kimbring2/DeepSoccer/deepsoccer_jetson/image/NX_DC_Motor.png

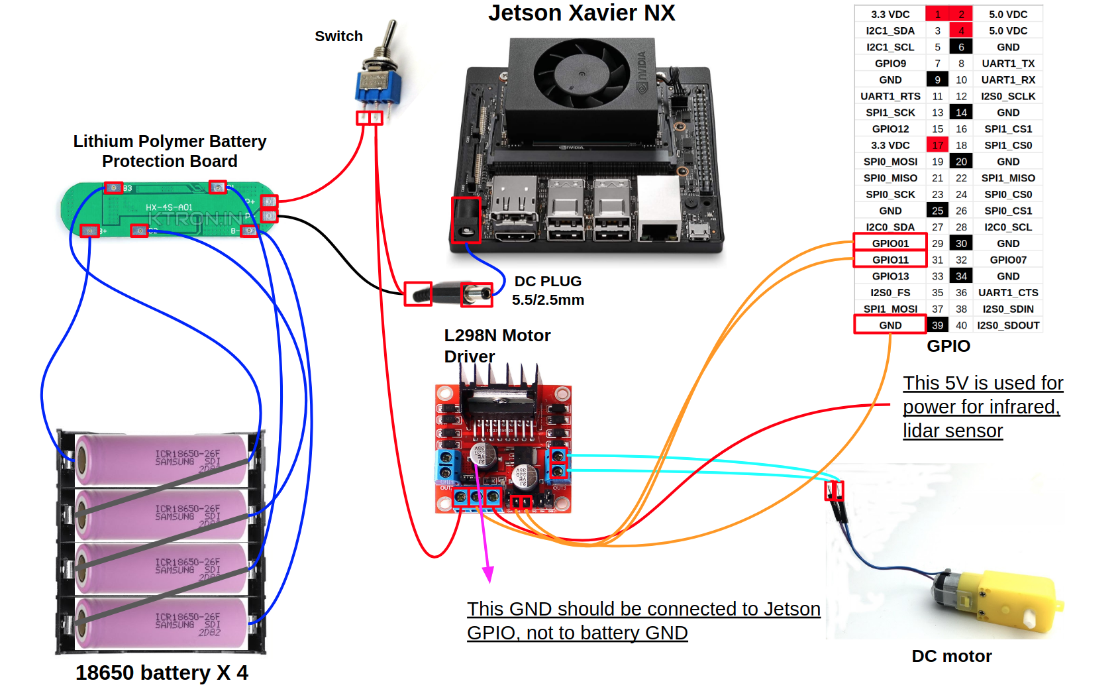
deepsoccer_jetson/image/NX_DC_Motor.png
