kimbring2/DeepSoccer/deepsoccer_jetson/image/NX_Dynamixel.png

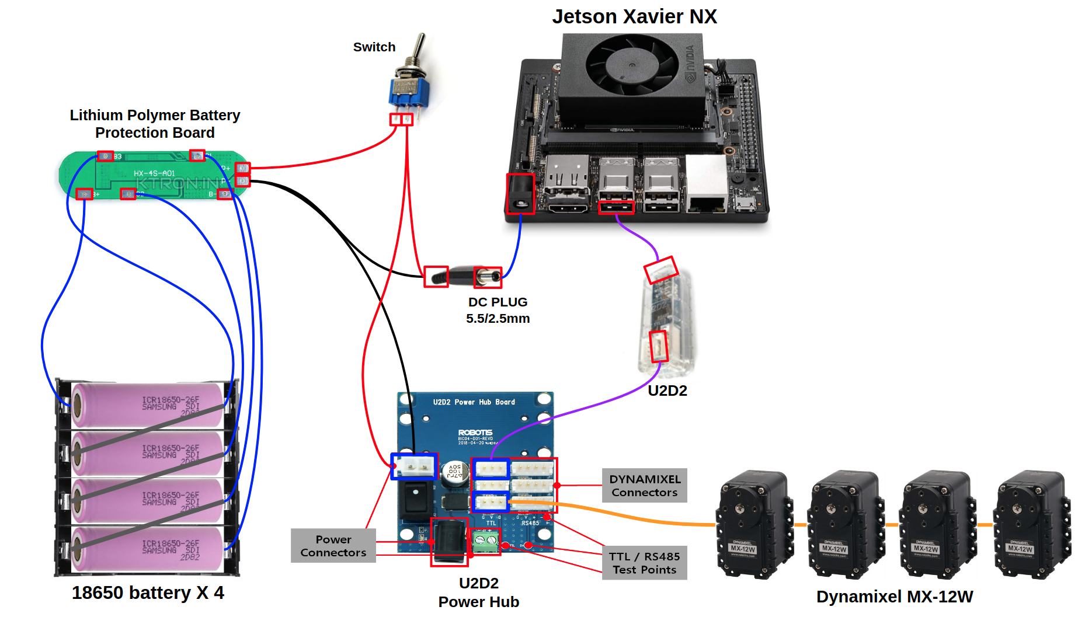
deepsoccer_jetson/image/NX_Dynamixel.png
