kimbring2/DeepSoccer/image/ADE_train_00006856.jpg

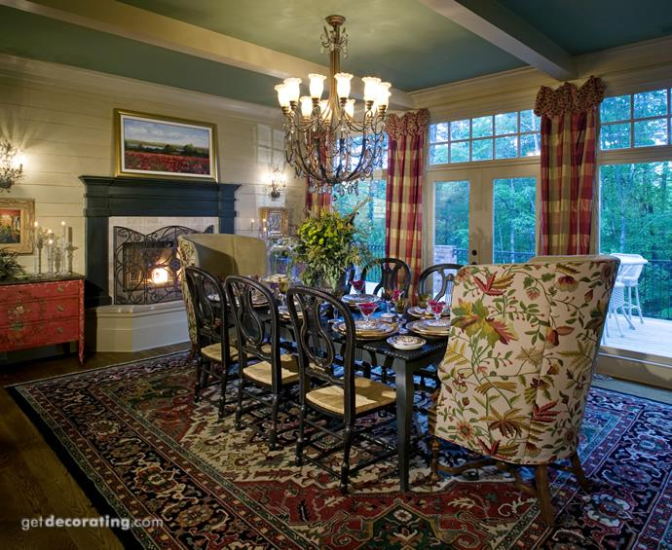
image/ADE_train_00006856.jpg
