kimbring2/DeepSoccer/image/ADE_train_00006856_seg.png

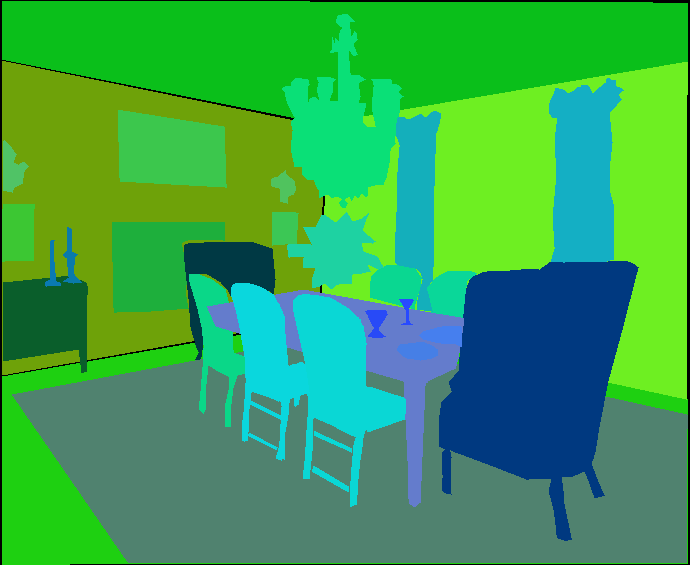
image/ADE_train_00006856_seg.png
