kimbring2/DeepSoccer/image/ADE_train_00006856_seg_simple.png

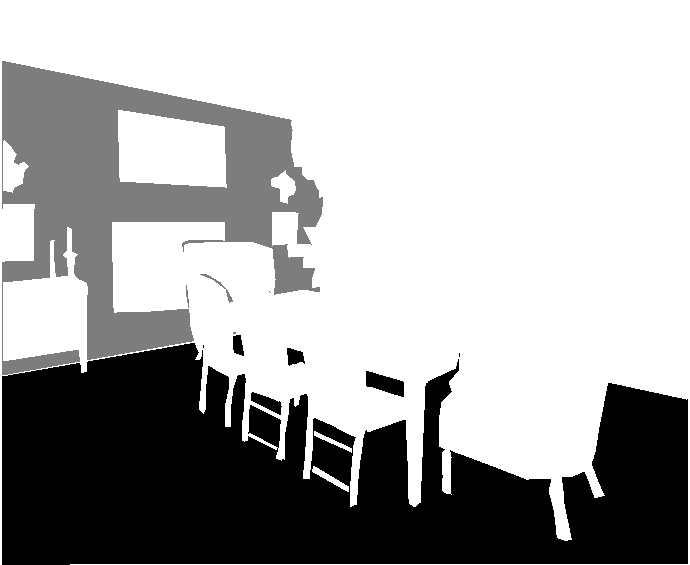
image/ADE_train_00006856_seg_simple.png
