kimbring2/DeepSoccer/image/controller_error.png

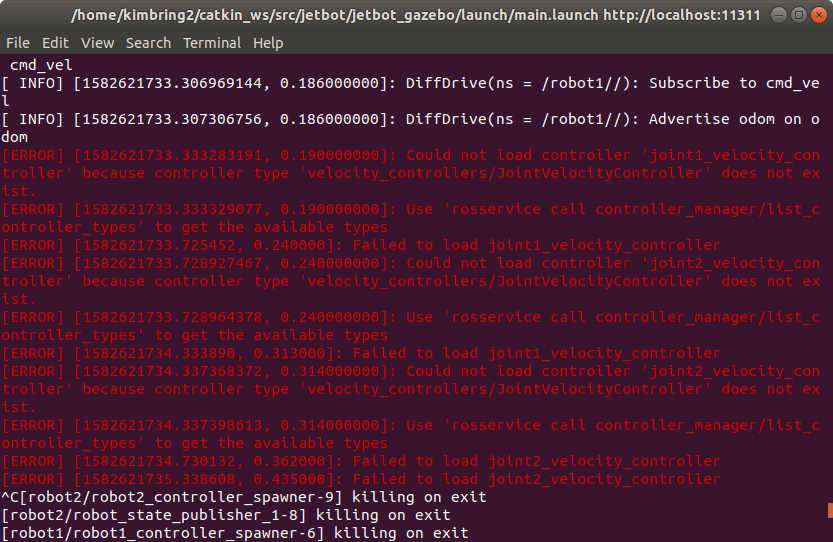
image/controller_error.png
