kimbring2/DeepSoccer/image/CycleGAN_wrong_case_4.png

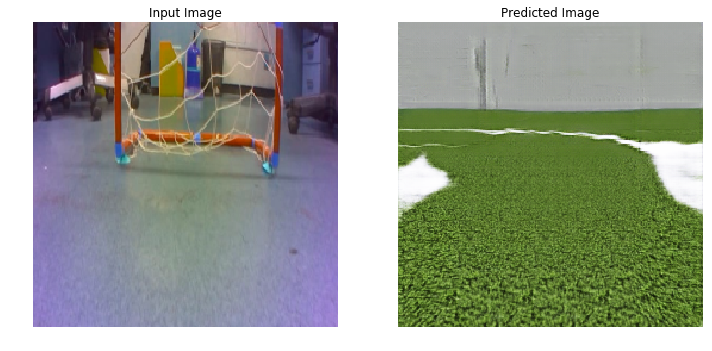
image/CycleGAN_wrong_case_4.png
