kimbring2/DeepSoccer/image/CycleGAN_wrong_case_7.png

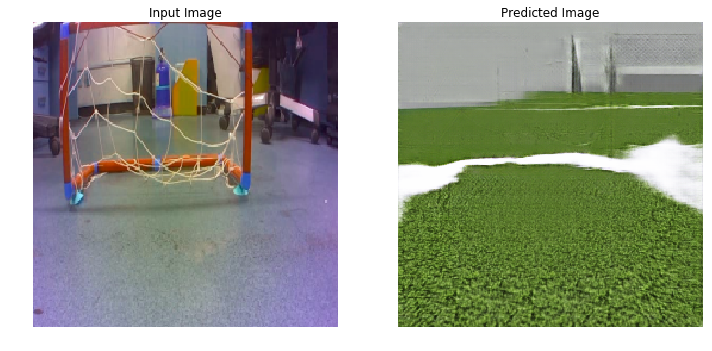
image/CycleGAN_wrong_case_7.png
