kimbring2/DeepSoccer/image/deepsoccer_reward.png

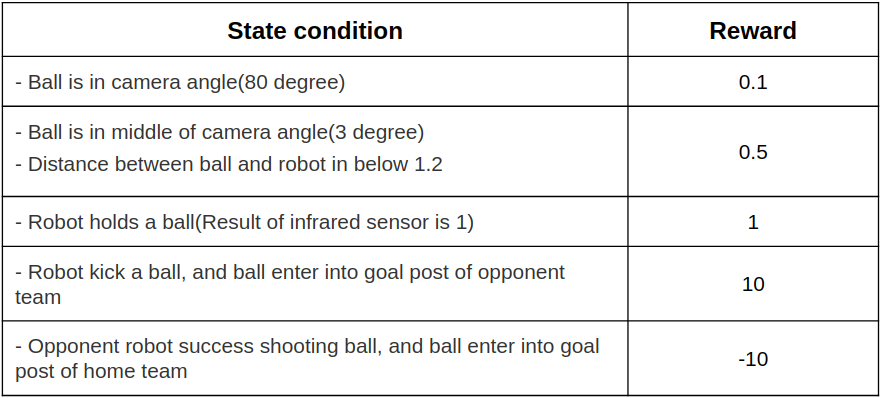
image/deepsoccer_reward.png
