kimbring2/DeepSoccer/image/dynamixel_connect.jpg

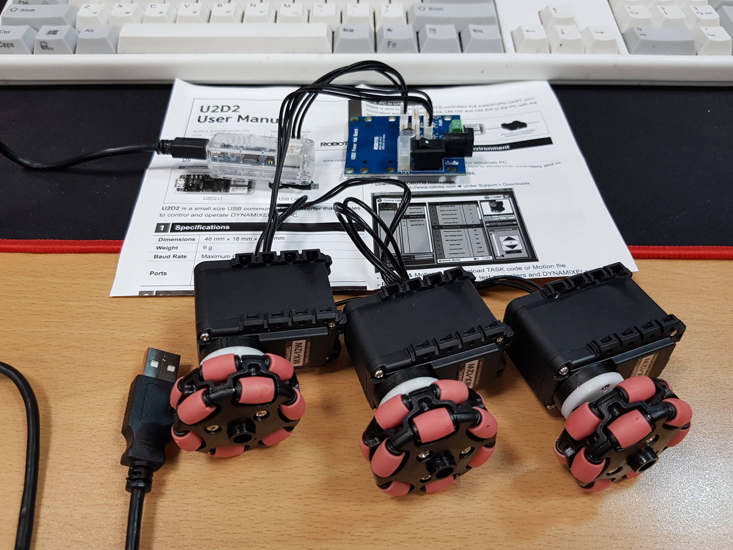
image/dynamixel_connect.jpg
