kimbring2/DeepSoccer/image/Error_Message.png

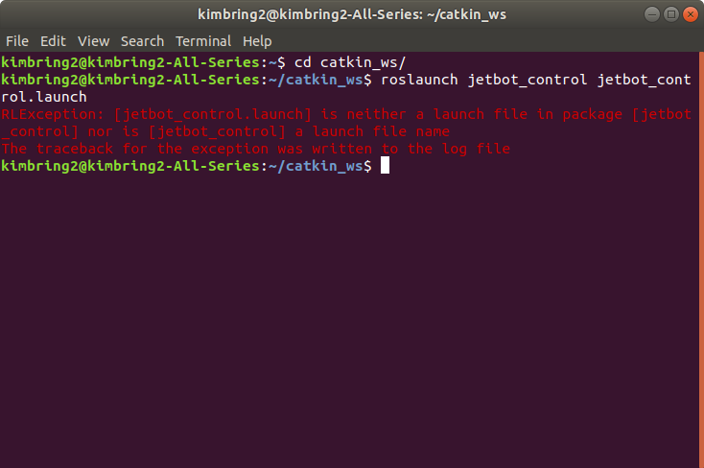
image/Error_Message.png
