kimbring2/DeepSoccer/image/jetbot_antenna_hori.png

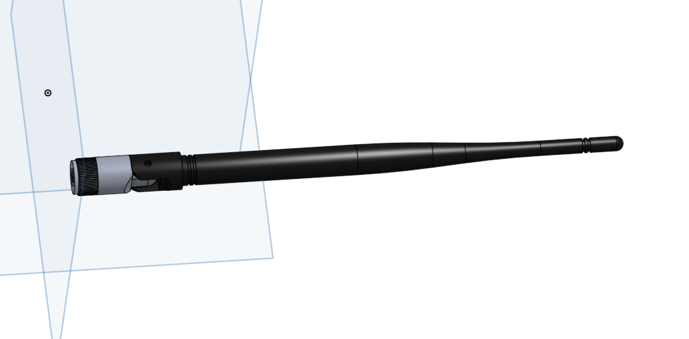
image/jetbot_antenna_hori.png
