kimbring2/DeepSoccer/image/jetbot_board.png

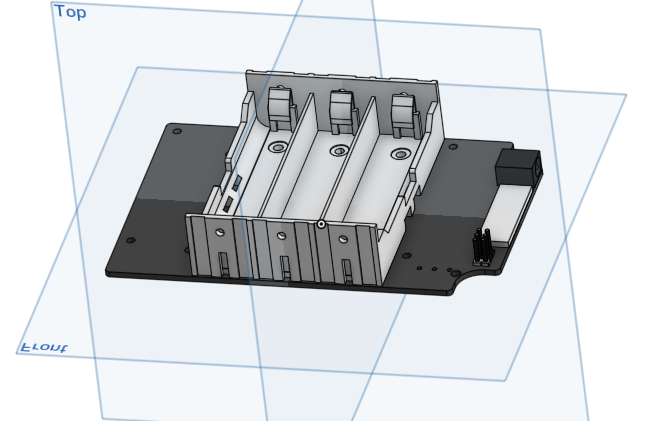
image/jetbot_board.png
