kimbring2/DeepSoccer/image/jetbot_dcmotor.png

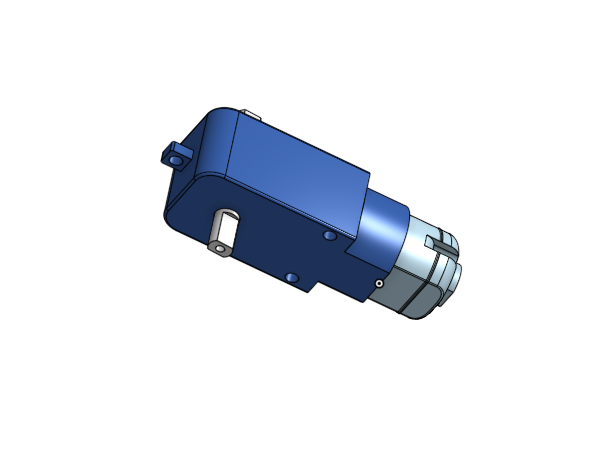
image/jetbot_dcmotor.png
