kimbring2/DeepSoccer/image/jetbot_frozen_graph.png

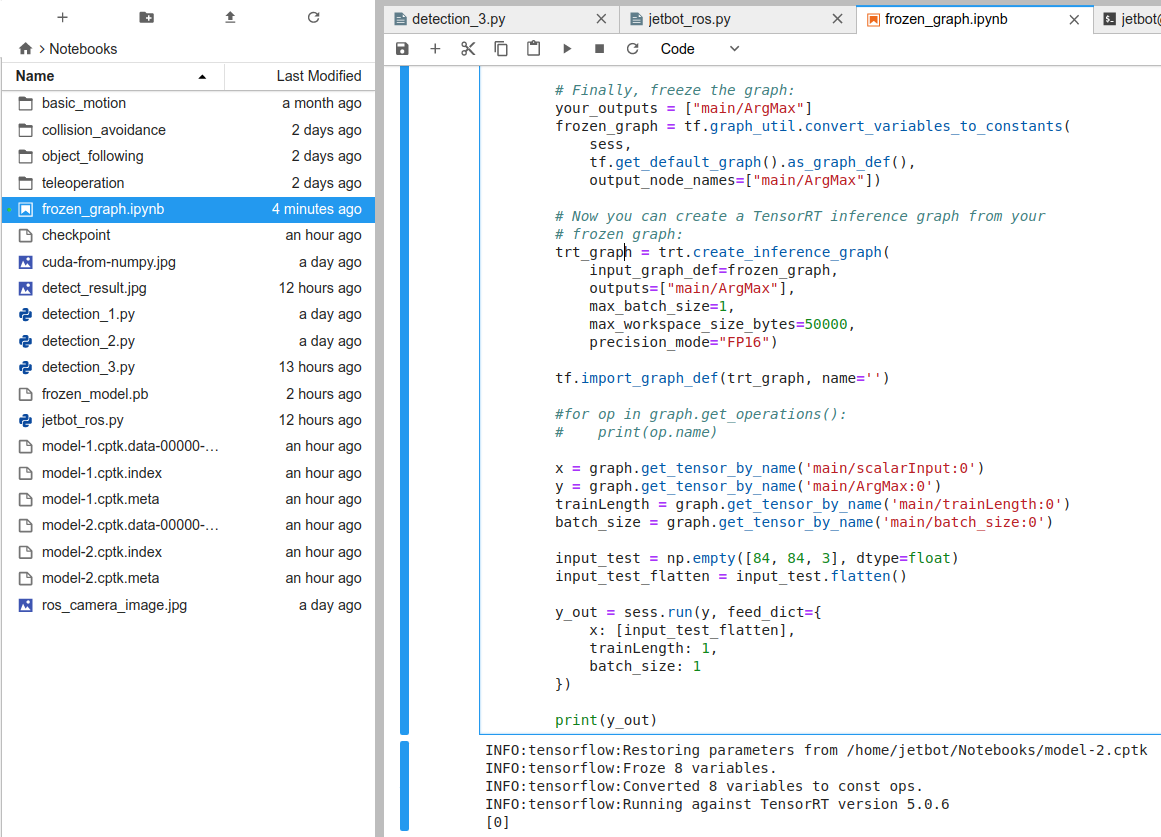
image/jetbot_frozen_graph.png
