kimbring2/DeepSoccer/image/jetbot_omniwheel.png

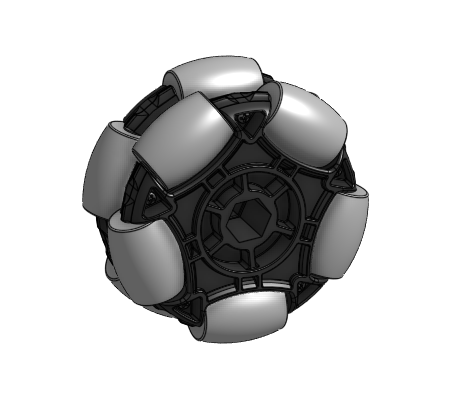
image/jetbot_omniwheel.png
