kimbring2/DeepSoccer/image/jetbot_resize_1.jpg

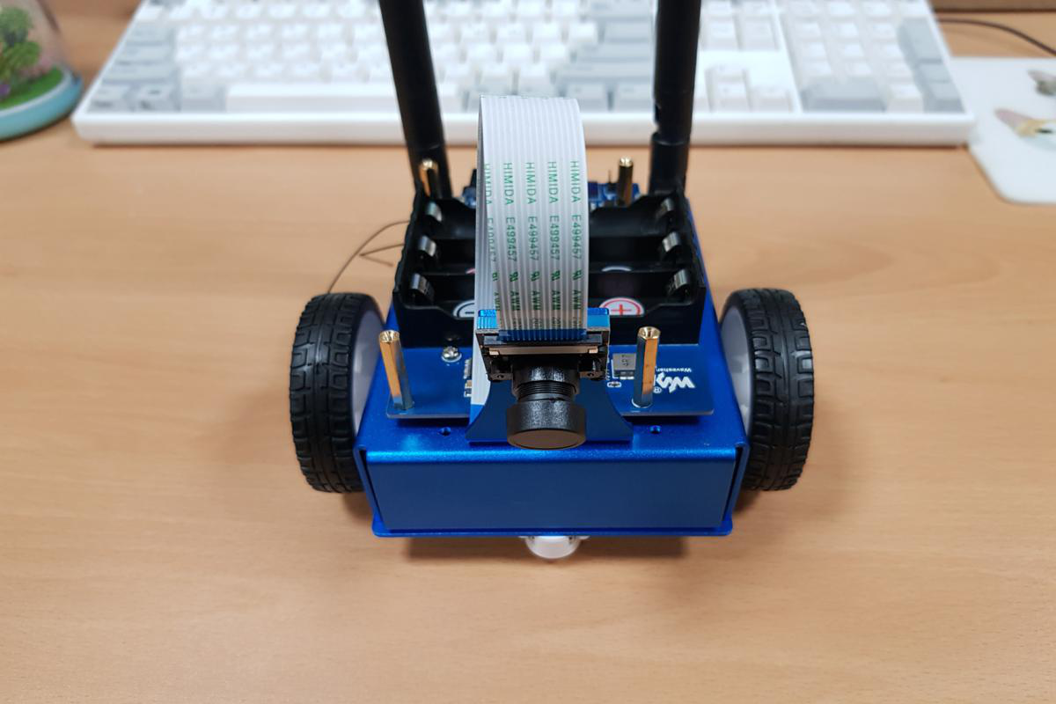
image/jetbot_resize_1.jpg
