kimbring2/DeepSoccer/image/jetbot_resize_2.jpg

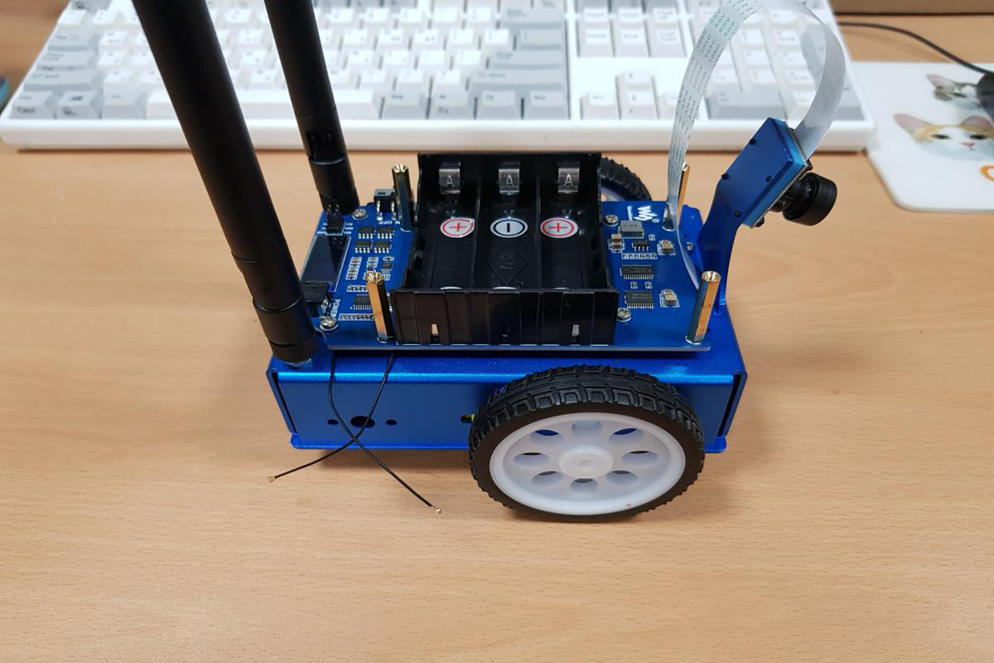
image/jetbot_resize_2.jpg
