kimbring2/DeepSoccer/image/jetbot_soccer.png

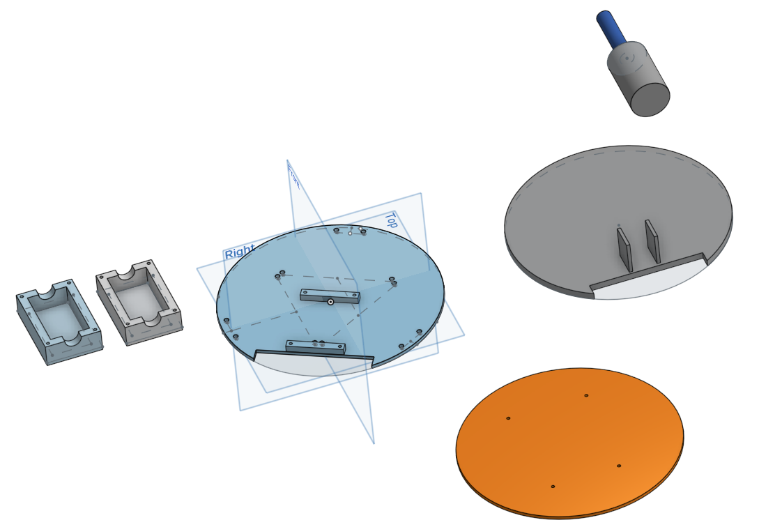
image/jetbot_soccer.png
