kimbring2/DeepSoccer/image/jetbot_soccer_1.png

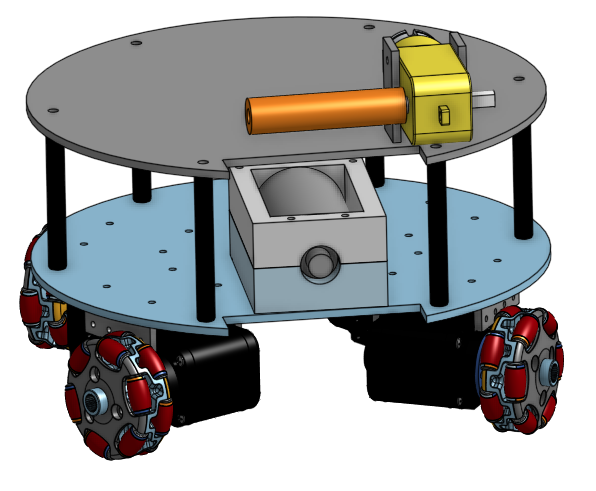
image/jetbot_soccer_1.png
