kimbring2/DeepSoccer/image/jetbot_soccer_proto_1.png

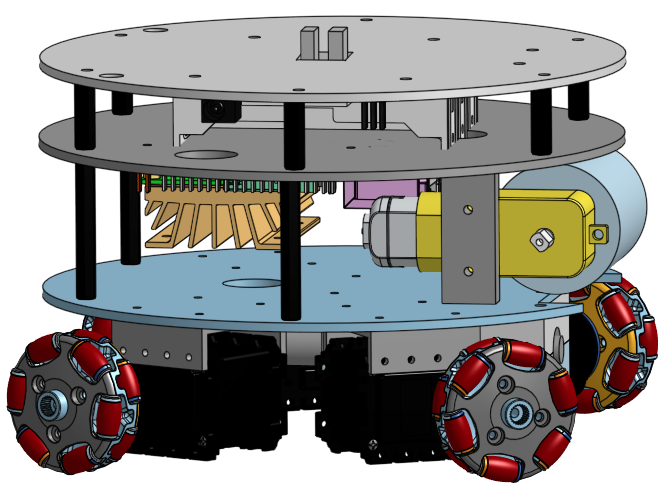
image/jetbot_soccer_proto_1.png
