kimbring2/DeepSoccer/image/jetbot_soccer_proto_2.png

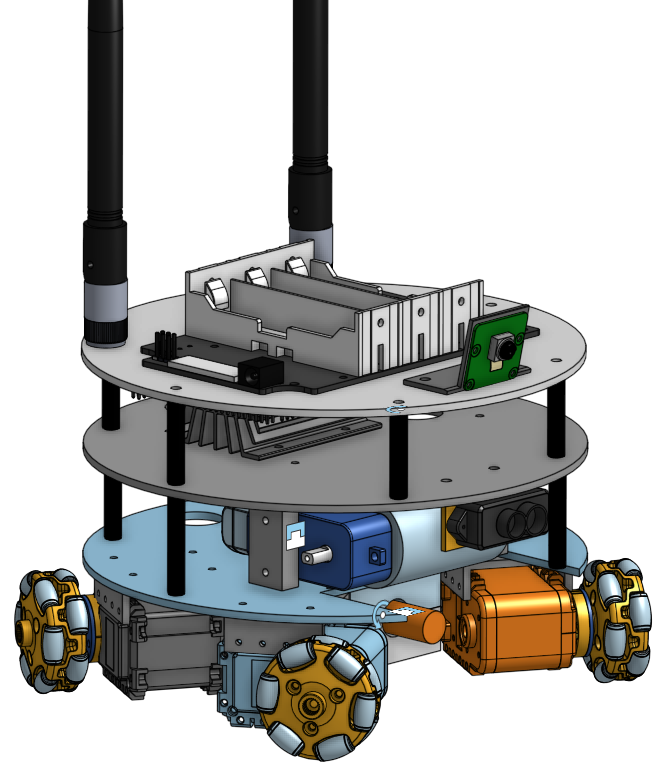
image/jetbot_soccer_proto_2.png
