kimbring2/DeepSoccer/image/joint_state_error.jpg

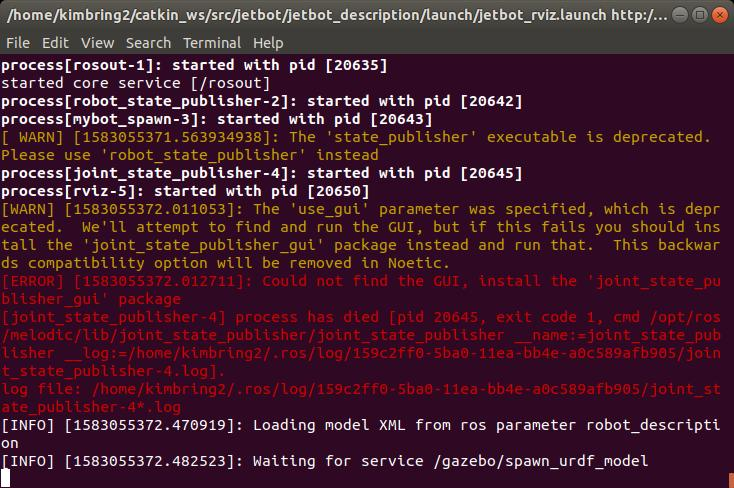
image/joint_state_error.jpg
