kimbring2/DeepSoccer/image/model_freezing.png

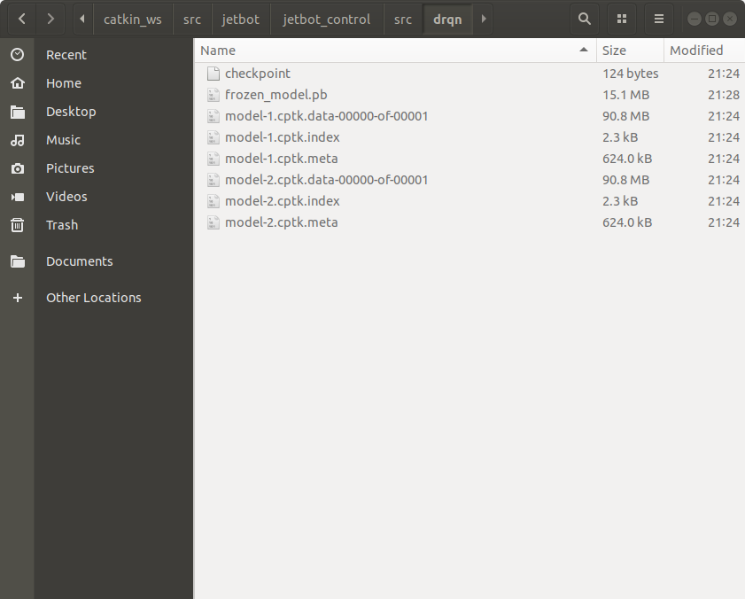
image/model_freezing.png
