kimbring2/DeepSoccer/image/NX_Display.png

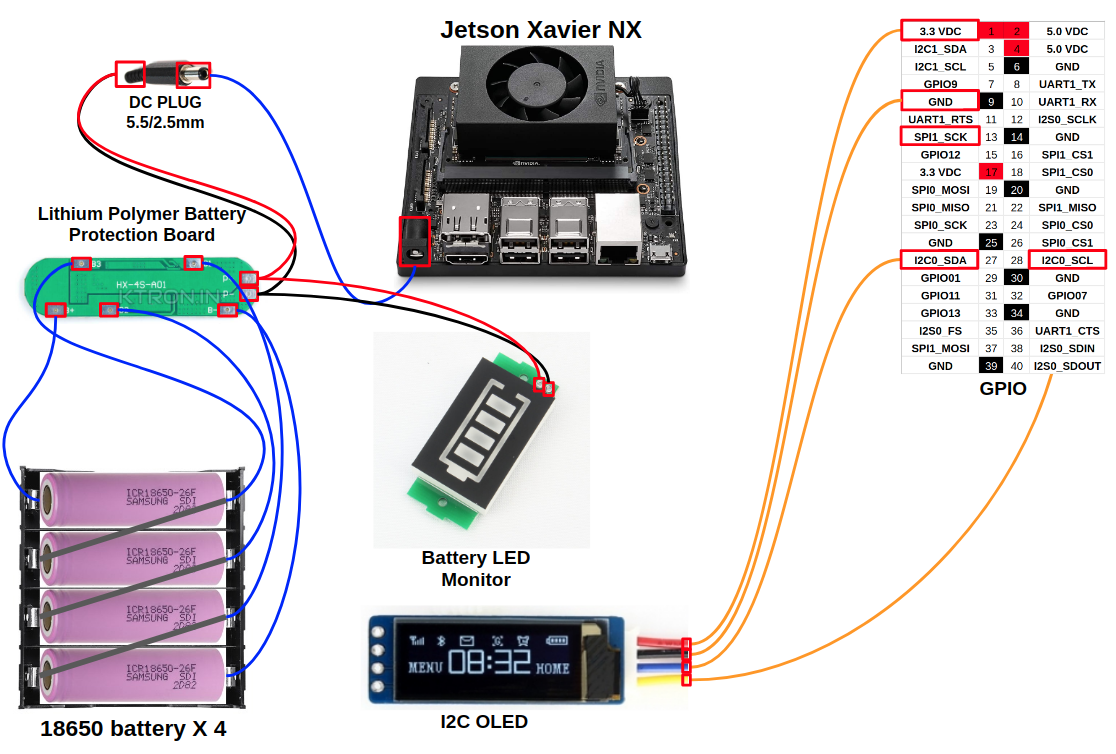
image/NX_Display.png
