kimbring2/DeepSoccer/image/raw-video.gif

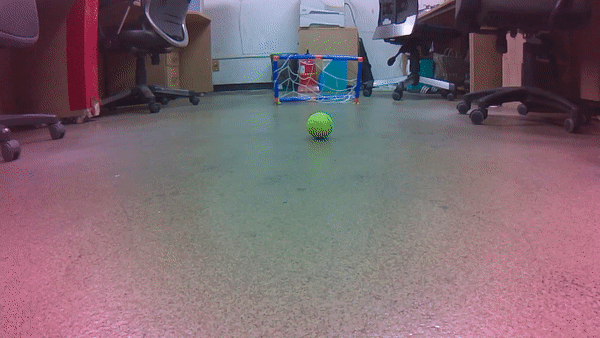
image/raw-video.gif
