kimbring2/DeepSoccer/image/robocup.jpg

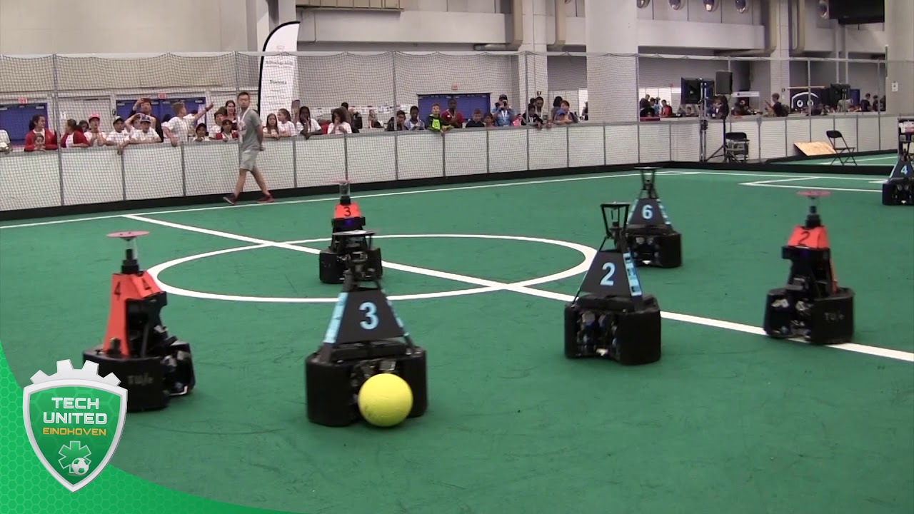
image/robocup.jpg
