kimbring2/DeepSoccer/image/rubber_roller.jpg

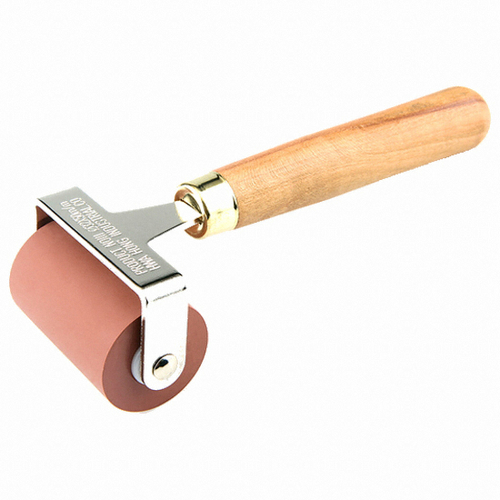
image/rubber_roller.jpg
