kimbring2/DeepSoccer/image/rw_setting.png

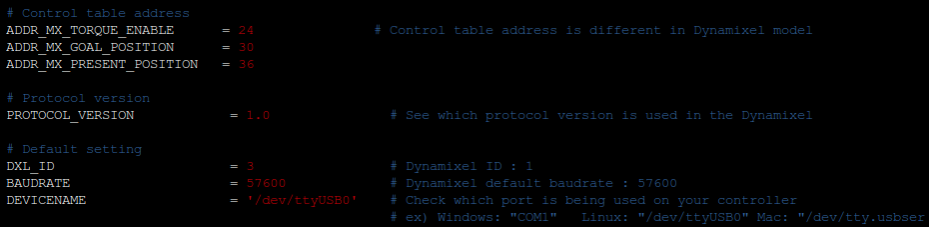
image/rw_setting.png
