kimbring2/DeepSoccer/image/rw_success.png

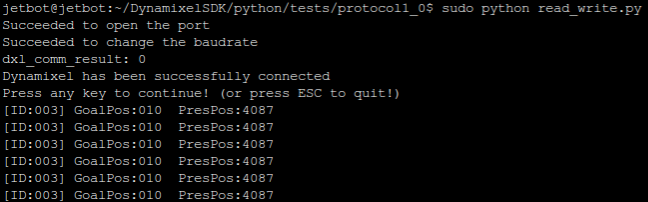
image/rw_success.png
