kimbring2/DeepSoccer/image/sim2real_frame.png

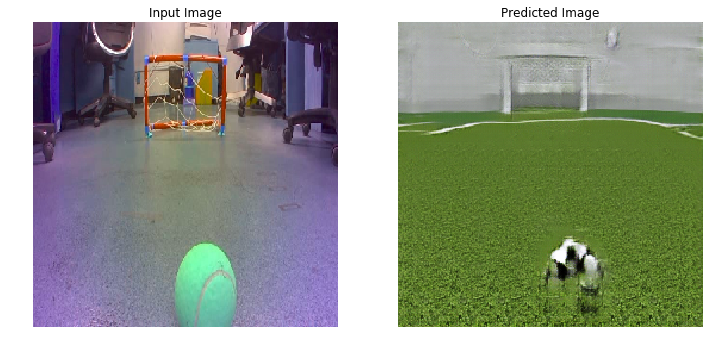
image/sim2real_frame.png
