kimbring2/DeepSoccer/image/solenoid_motor.jpg

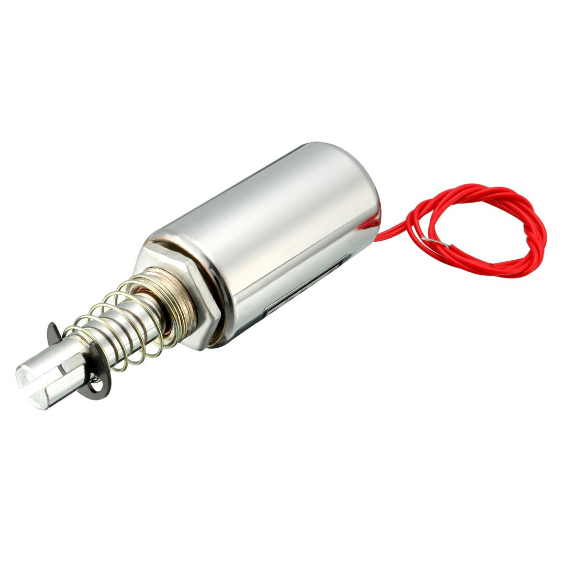
image/solenoid_motor.jpg
