kimbring2/DeepSoccer/image/Spring-Constant.jpg

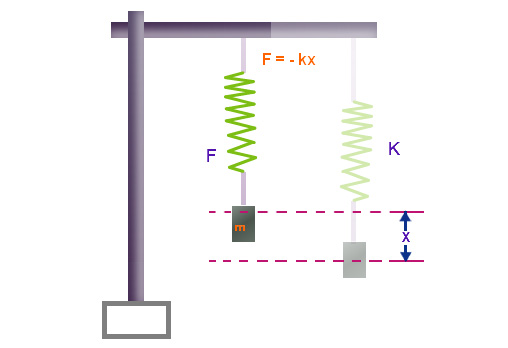
image/Spring-Constant.jpg
