kimbring2/DeepSoccer/image/styled-video.gif

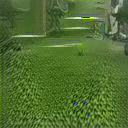
image/styled-video.gif
