kimbring2/DeepSoccer/image/teleoperation_ps4.png

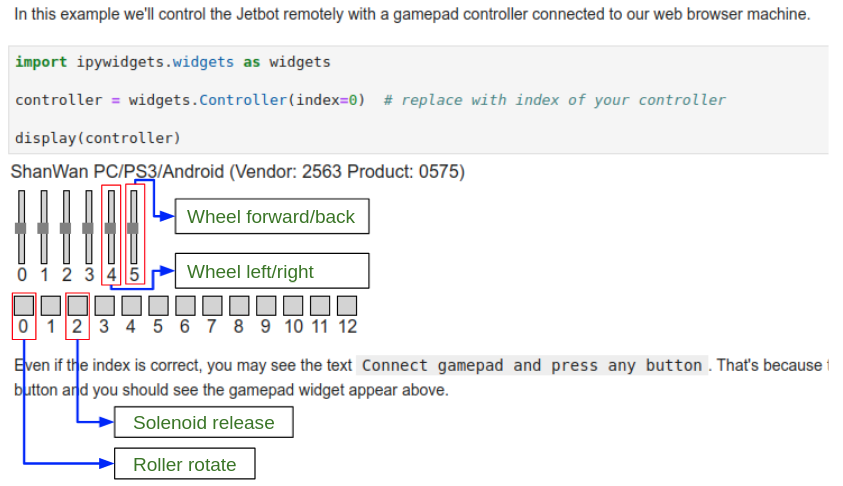
image/teleoperation_ps4.png
