kimbring2/DeepSoccer/sim2real/content_image.jpg

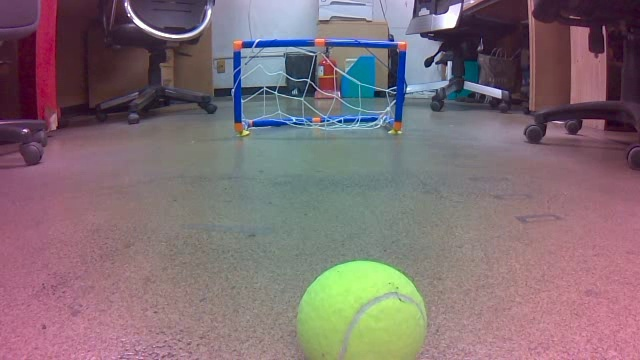
sim2real/content_image.jpg
