kimbring2/DeepSoccer/deepsoccer_pc/deepsoccer_description/urdf/deepsoccer/solenoid_body.stl

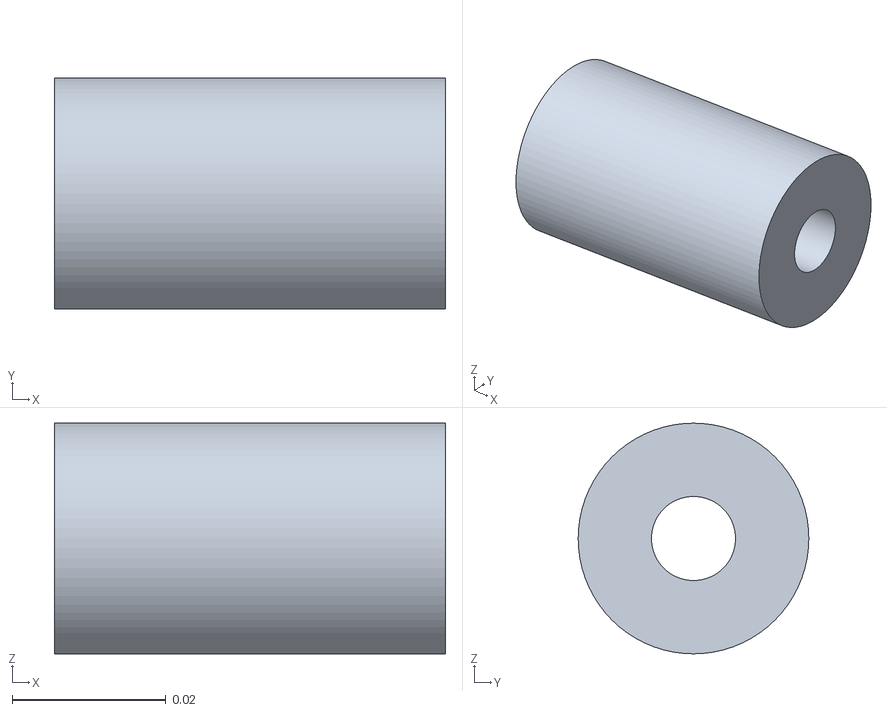
[picture p66: CAD file, 2020-08-27]
deepsoccer_pc/deepsoccer_description/urdf/deepsoccer/solenoid_body.stl
0.0508 x 0.03 x 0.03
