kimbring2/DeepSoccer/deepsoccer_pc/deepsoccer_description/urdf/deepsoccer/lidar_sensor_1.stl

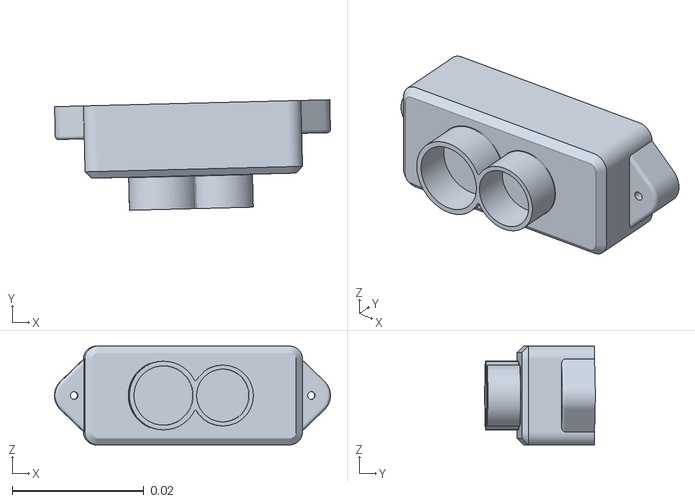
[picture p67: CAD file, 2020-08-27]
deepsoccer_pc/deepsoccer_description/urdf/deepsoccer/lidar_sensor_1.stl
0.0419 x 0.0168 x 0.015
