kimbring2/DeepSoccer/deepsoccer_pc/deepsoccer_description/urdf/deepsoccer/lidar_frame_1.stl

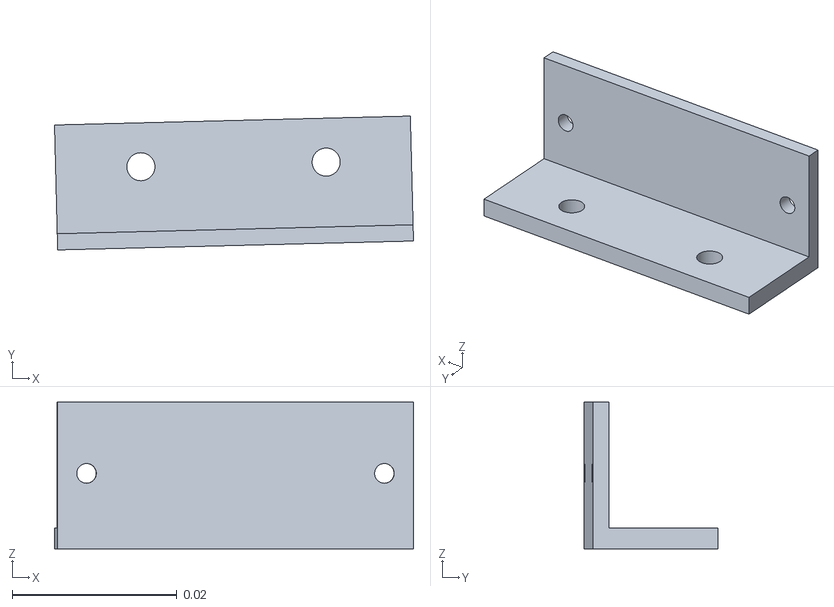
[picture p68: CAD file, 2020-08-27]
deepsoccer_pc/deepsoccer_description/urdf/deepsoccer/lidar_frame_1.stl
0.0435 x 0.0162 x 0.0178
