kimbring2/DeepSoccer/deepsoccer_pc/deepsoccer_description/urdf/deepsoccer/antenna_2.stl

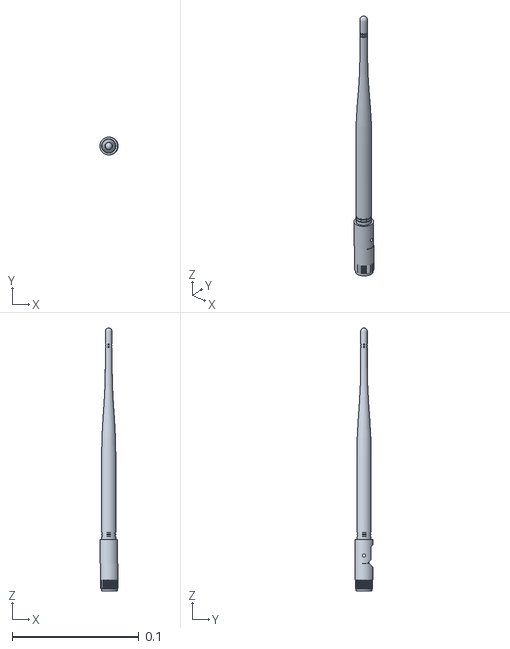
[picture p69: CAD file, 2020-08-27]
deepsoccer_pc/deepsoccer_description/urdf/deepsoccer/antenna_2.stl
0.0145 x 0.014 x 0.207
