kimbring2/DeepSoccer/deepsoccer_pc/deepsoccer_description/urdf/deepsoccer/body_2.stl

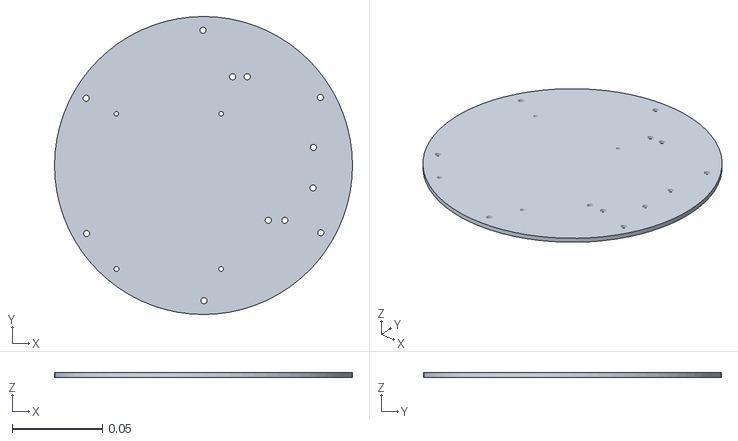
[picture p70: CAD file, 2020-08-27]
deepsoccer_pc/deepsoccer_description/urdf/deepsoccer/body_2.stl
0.165 x 0.165 x 0.00254
