kimbring2/DeepSoccer/deepsoccer_pc/deepsoccer_description/urdf/deepsoccer/camera_holder_1.stl

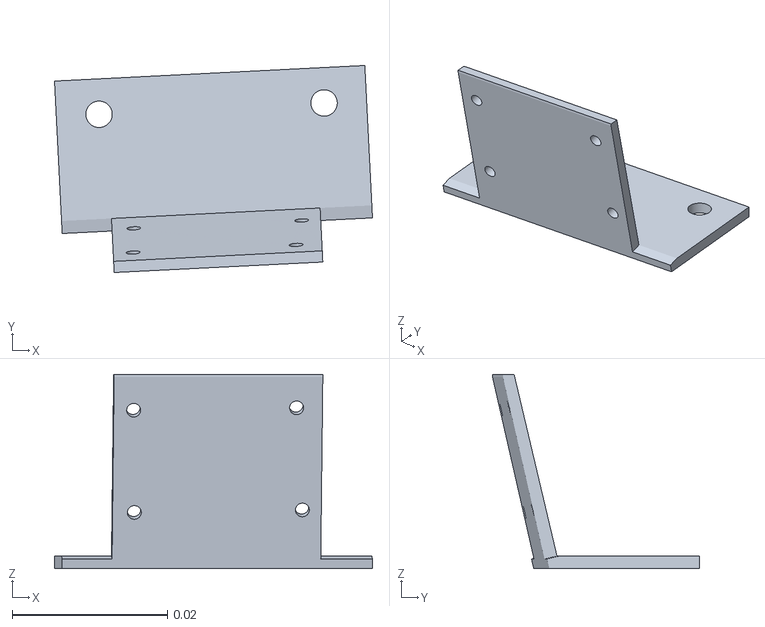
[picture p71: CAD file, 2020-08-27]
deepsoccer_pc/deepsoccer_description/urdf/deepsoccer/camera_holder_1.stl
0.0409 x 0.0267 x 0.025
