kimbring2/DeepSoccer/deepsoccer_pc/deepsoccer_description/urdf/deepsoccer/roller_stick_1.stl

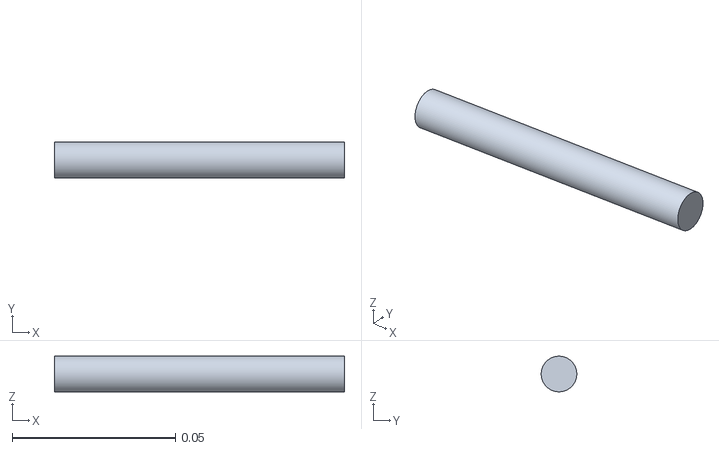
[picture p72: CAD file, 2020-08-27]
deepsoccer_pc/deepsoccer_description/urdf/deepsoccer/roller_stick_1.stl
0.0889 x 0.0109 x 0.0109
