kimbring2/DeepSoccer/deepsoccer_pc/deepsoccer_description/urdf/deepsoccer/roller_1.stl

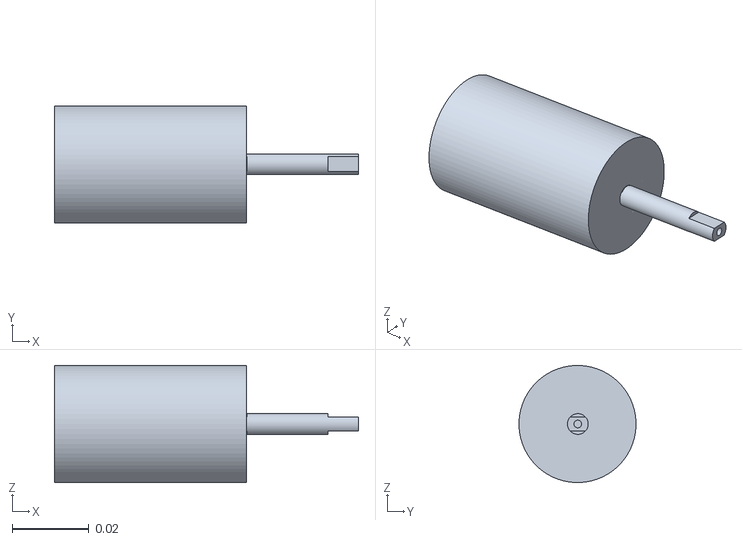
[picture p73: CAD file, 2020-08-27]
deepsoccer_pc/deepsoccer_description/urdf/deepsoccer/roller_1.stl
0.0791 x 0.0305 x 0.0305
