kimbring2/DeepSoccer/deepsoccer_pc/deepsoccer_description/urdf/deepsoccer/rspcameramia_1.stl

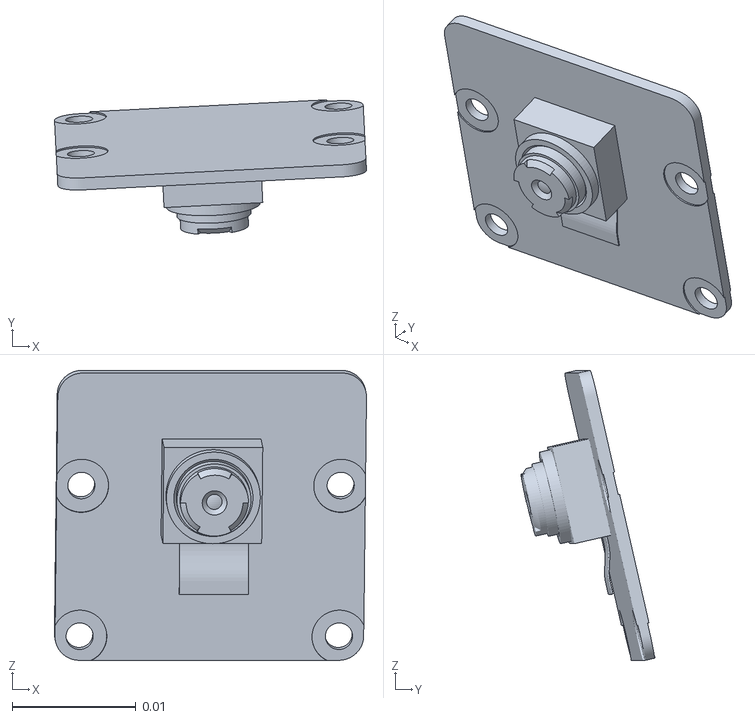
[picture p74: CAD file, 2020-08-27]
deepsoccer_pc/deepsoccer_description/urdf/deepsoccer/rspcameramia_1.stl
0.0252 x 0.0109 x 0.0235
