kimbring2/DeepSoccer/deepsoccer_pc/deepsoccer_description/urdf/deepsoccer/part_1.stl

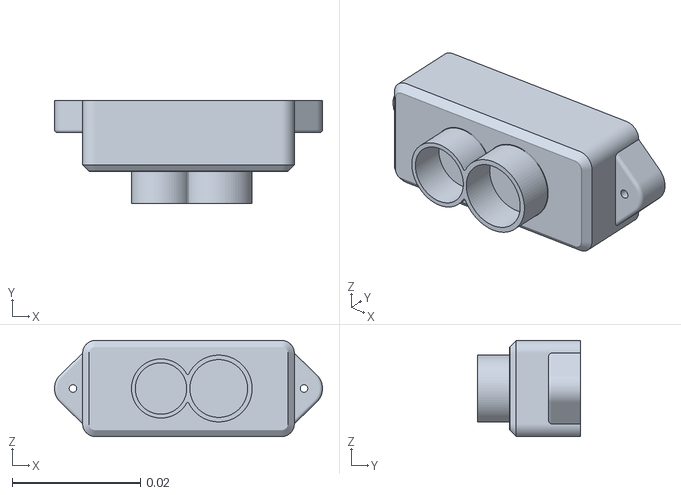
[picture p75: CAD file, 2020-05-21]
deepsoccer_pc/deepsoccer_description/urdf/deepsoccer/part_1.stl
0.0418 x 0.016 x 0.015
