kimbring2/DeepSoccer/deepsoccer_pc/deepsoccer_description/urdf/deepsoccer/chipset.stl

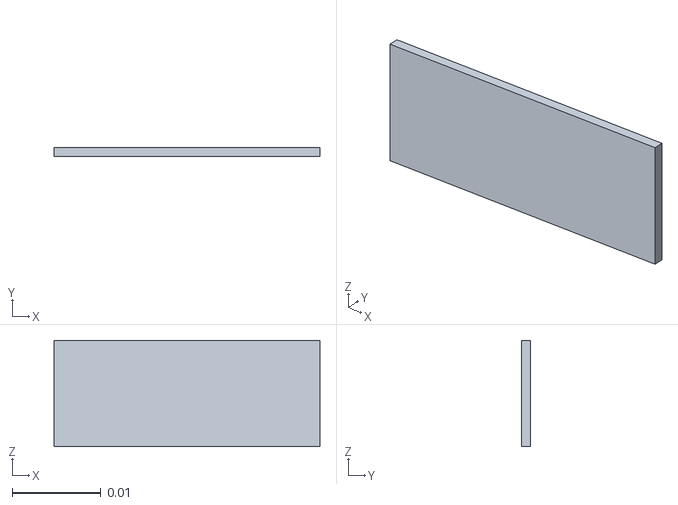
[picture p76: CAD file, 2020-05-21]
deepsoccer_pc/deepsoccer_description/urdf/deepsoccer/chipset.stl
0.03 x 0.001 x 0.012
