kimbring2/DeepSoccer/deepsoccer_pc/deepsoccer_description/urdf/deepsoccer/part_13.stl

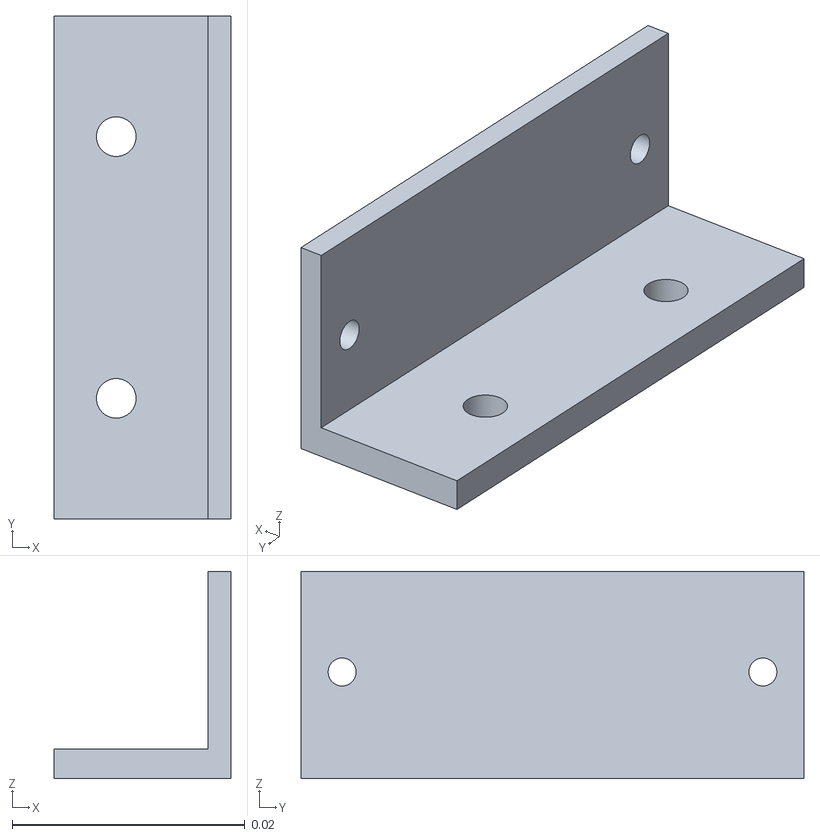
[picture p77: CAD file, 2020-05-21]
deepsoccer_pc/deepsoccer_description/urdf/deepsoccer/part_13.stl
0.0152 x 0.0432 x 0.0178
