kimbring2/DeepSoccer/deepsoccer_pc/deepsoccer_description/urdf/deepsoccer/sm04b-ghs-tb.stl

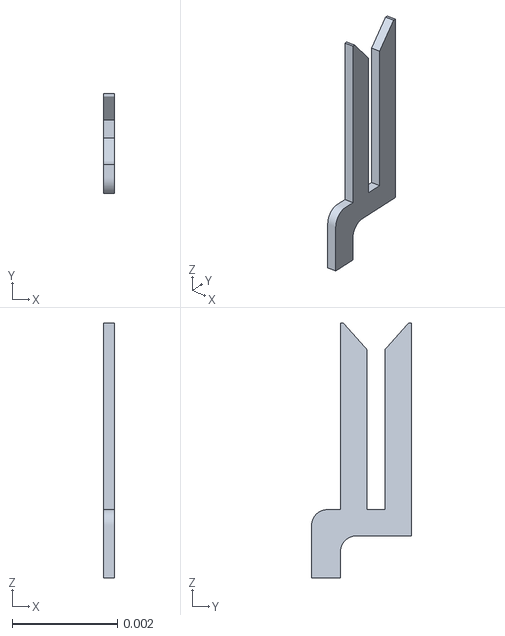
[picture p78: CAD file, 2020-05-21]
deepsoccer_pc/deepsoccer_description/urdf/deepsoccer/sm04b-ghs-tb.stl
0.0002 x 0.0019 x 0.00485
