kimbring2/DeepSoccer/deepsoccer_pc/deepsoccer_description/urdf/deepsoccer/adesivo.stl

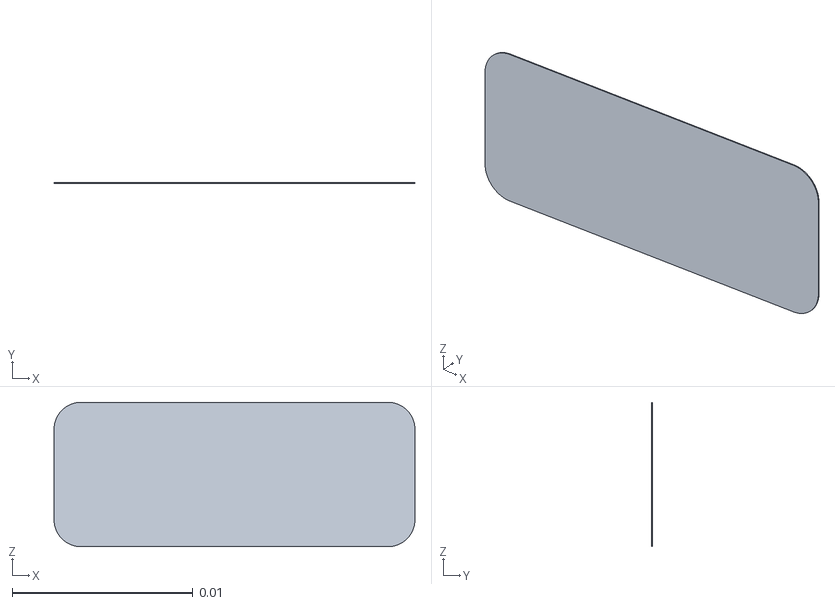
[picture p79: CAD file, 2020-05-21]
deepsoccer_pc/deepsoccer_description/urdf/deepsoccer/adesivo.stl
0.02 x 5e-05 x 0.008
