kimbring2/DeepSoccer/deepsoccer_pc/deepsoccer_description/urdf/deepsoccer/lente_pequena.stl

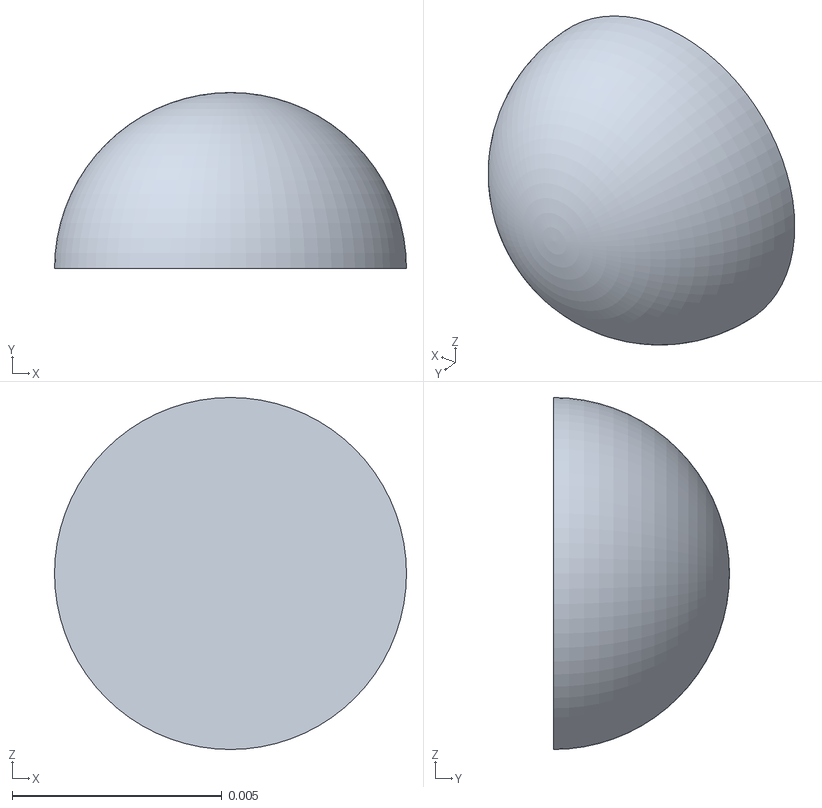
[picture p80: CAD file, 2020-05-21]
deepsoccer_pc/deepsoccer_description/urdf/deepsoccer/lente_pequena.stl
0.0084 x 0.0042 x 0.0084
