kimbring2/DeepSoccer/deepsoccer_pc/deepsoccer_description/urdf/deepsoccer/lidar_benewake_tfmini.stl

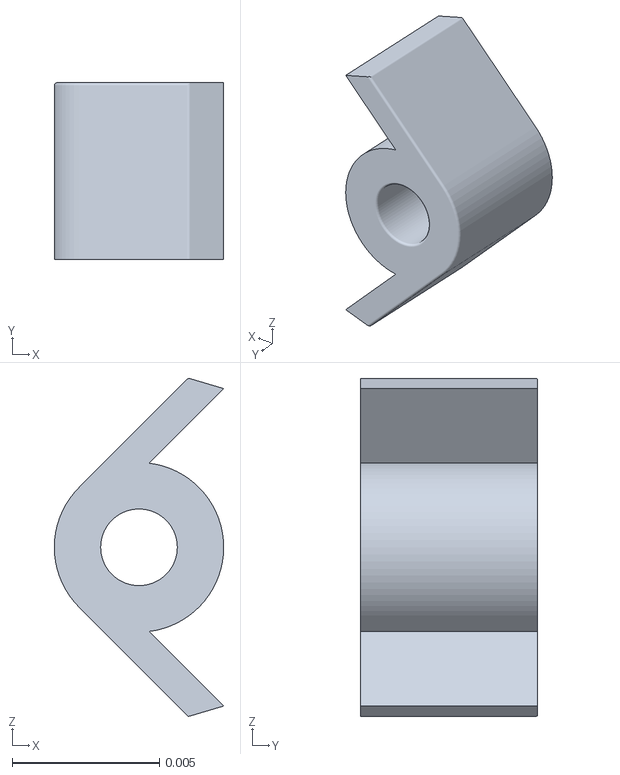
[picture p81: CAD file, 2020-05-21]
deepsoccer_pc/deepsoccer_description/urdf/deepsoccer/lidar_benewake_tfmini.stl
0.00575 x 0.006 x 0.0115
