kimbring2/DeepSoccer/deepsoccer_pc/deepsoccer_description/urdf/deepsoccer/lente_grande.stl

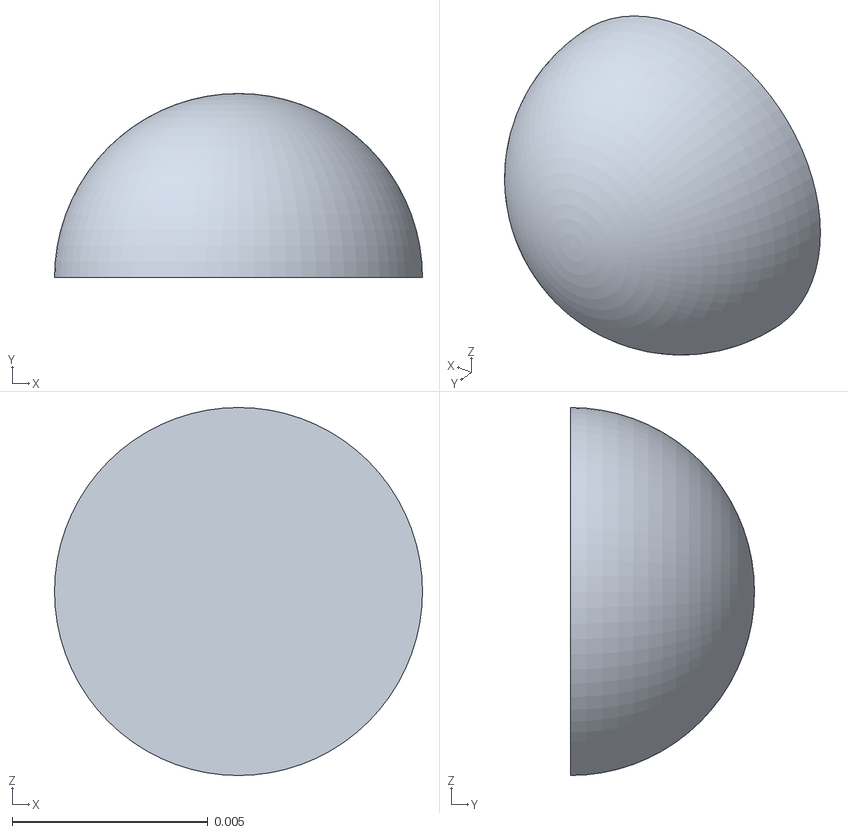
[picture p82: CAD file, 2020-05-21]
deepsoccer_pc/deepsoccer_description/urdf/deepsoccer/lente_grande.stl
0.0094 x 0.0047 x 0.0094
