kimbring2/DeepSoccer/deepsoccer_pc/deepsoccer_description/urdf/deepsoccer/document.stl

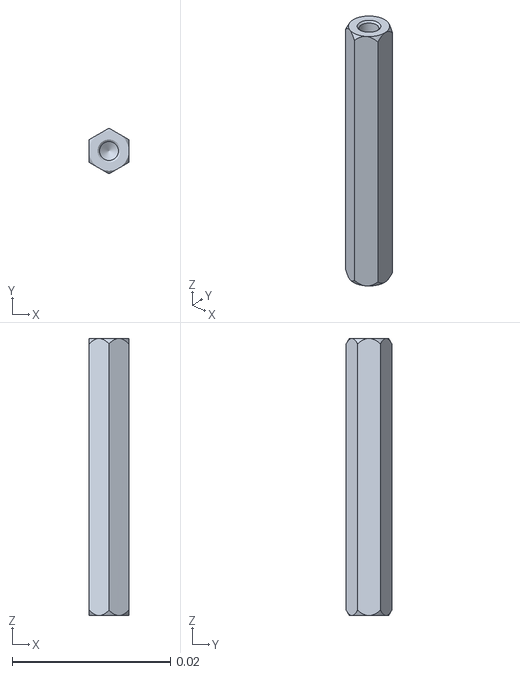
[picture p83: CAD file, 2020-03-06]
deepsoccer_pc/deepsoccer_description/urdf/deepsoccer/document.stl
0.005 x 0.00577 x 0.035
