kimbring2/DeepSoccer/deepsoccer_pc/deepsoccer_description/urdf/deepsoccer/roller.stl

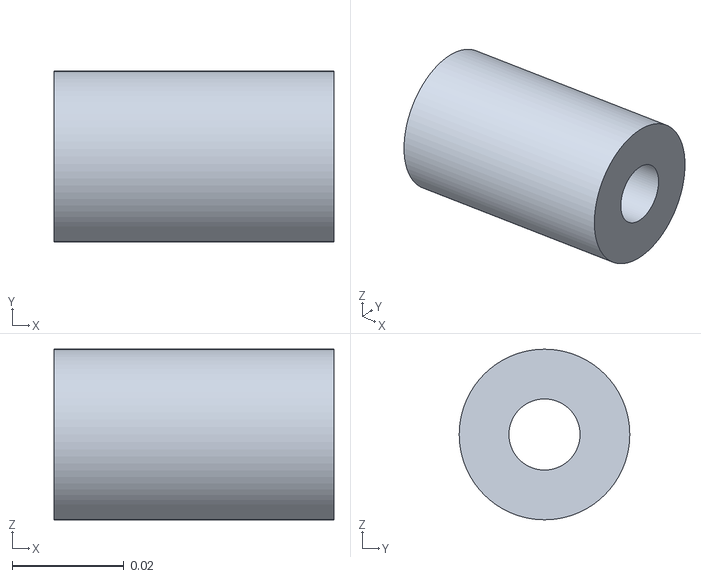
[picture p84: CAD file, 2020-03-06]
deepsoccer_pc/deepsoccer_description/urdf/deepsoccer/roller.stl
0.05 x 0.0305 x 0.0305
