kimbring2/DeepSoccer/deepsoccer_pc/deepsoccer_description/urdf/deepsoccer/capc-0402-t0.55-bn.stl

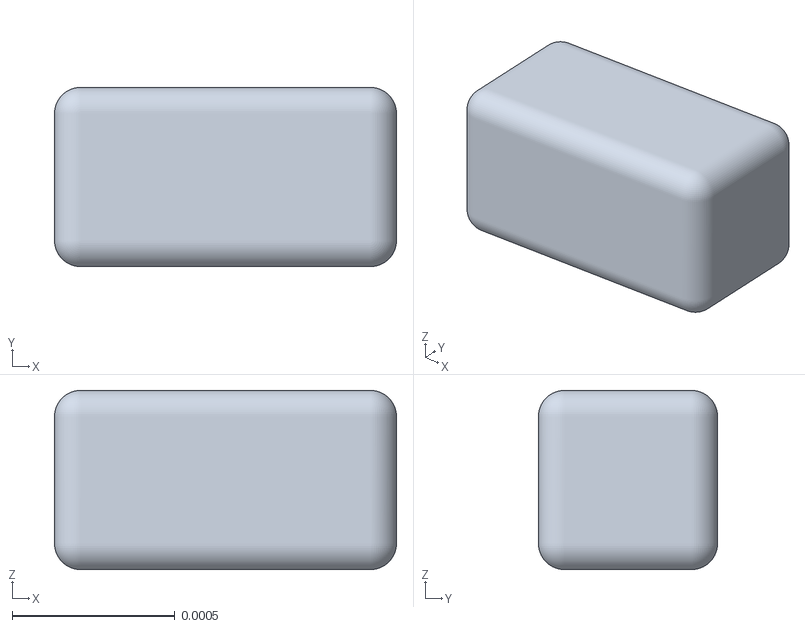
[picture p85: CAD file, 2020-03-03]
deepsoccer_pc/deepsoccer_description/urdf/deepsoccer/capc-0402-t0.55-bn.stl
0.00105 x 0.00055 x 0.00055
