kimbring2/DeepSoccer/deepsoccer_pc/deepsoccer_description/urdf/deepsoccer/ova5647_lens_fov.stl

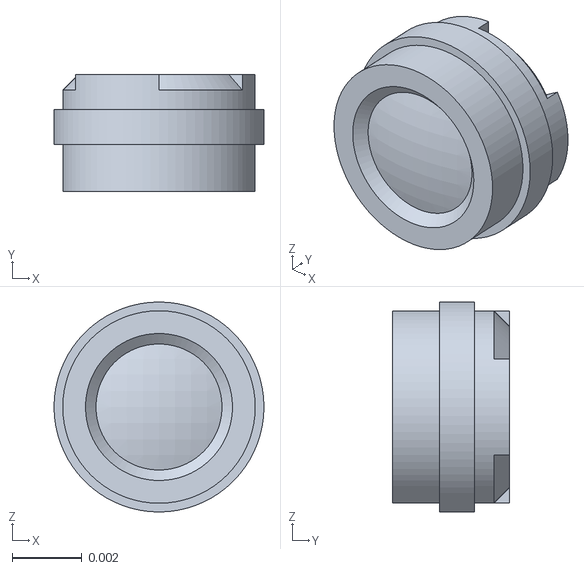
[picture p86: CAD file, 2020-03-03]
deepsoccer_pc/deepsoccer_description/urdf/deepsoccer/ova5647_lens_fov.stl
0.006 x 0.00335 x 0.006
