kimbring2/DeepSoccer/deepsoccer_pc/deepsoccer_description/urdf/deepsoccer/ova5647_housing.stl

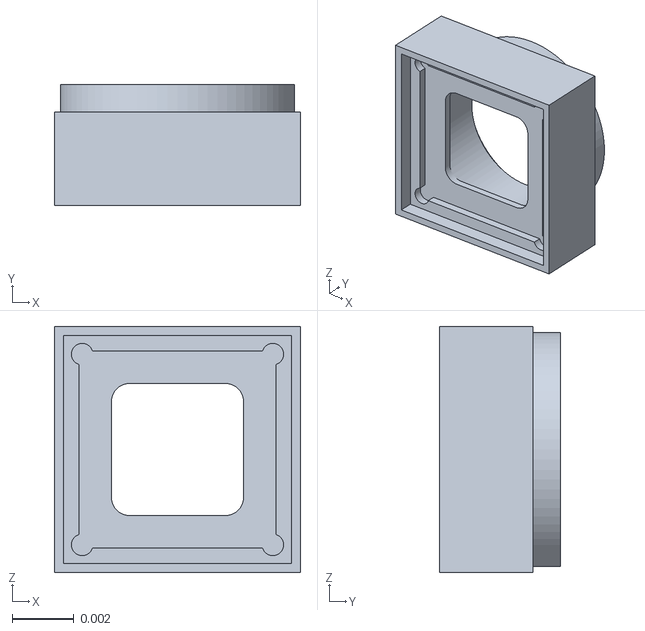
[picture p87: CAD file, 2020-03-03]
deepsoccer_pc/deepsoccer_description/urdf/deepsoccer/ova5647_housing.stl
0.008 x 0.00395 x 0.008
