kimbring2/DeepSoccer/deepsoccer_pc/deepsoccer_description/urdf/deepsoccer/c6aaa.stl

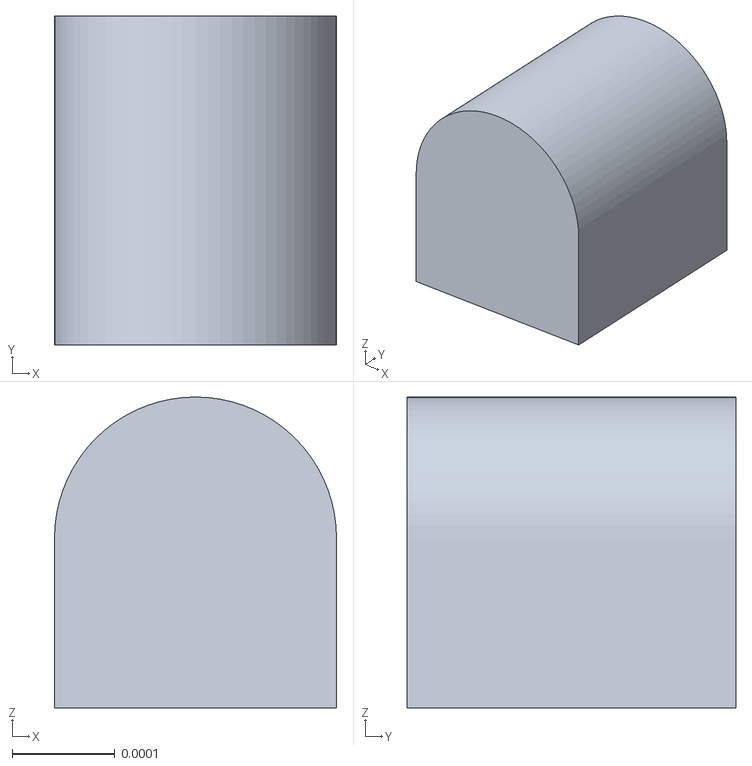
[picture p88: CAD file, 2020-03-03]
deepsoccer_pc/deepsoccer_description/urdf/deepsoccer/c6aaa.stl
0.000274 x 0.00032 x 0.000302
