kimbring2/DeepSoccer/deepsoccer_pc/deepsoccer_description/urdf/deepsoccer/picamerapcb.stl

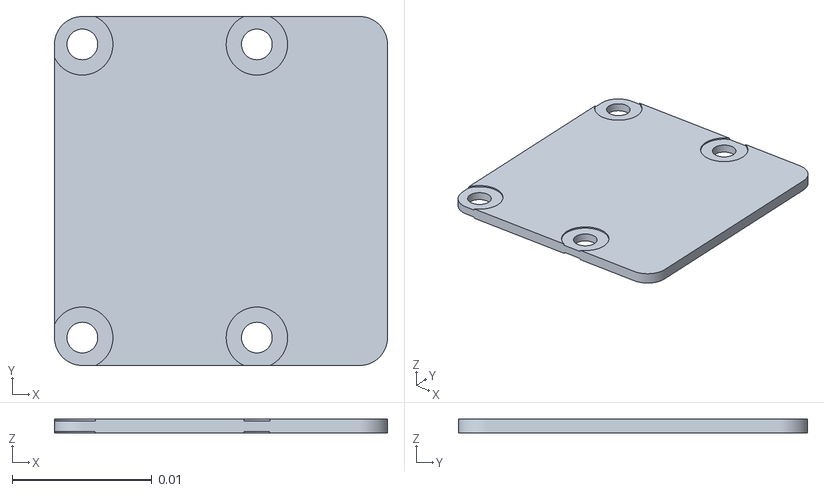
[picture p89: CAD file, 2020-03-03]
deepsoccer_pc/deepsoccer_description/urdf/deepsoccer/picamerapcb.stl
0.0239 x 0.025 x 0.001
