kimbring2/DeepSoccer/deepsoccer_pc/deepsoccer_description/urdf/deepsoccer/camera_holder.stl

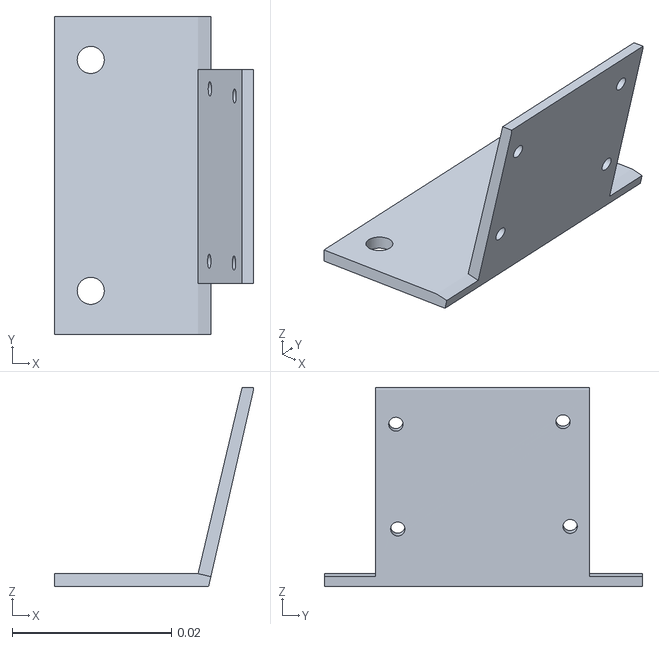
[picture p90: CAD file, 2020-03-03]
deepsoccer_pc/deepsoccer_description/urdf/deepsoccer/camera_holder.stl
0.025 x 0.04 x 0.025
