kimbring2/DeepSoccer/deepsoccer_pc/deepsoccer_description/urdf/deepsoccer/sot23-5.stl

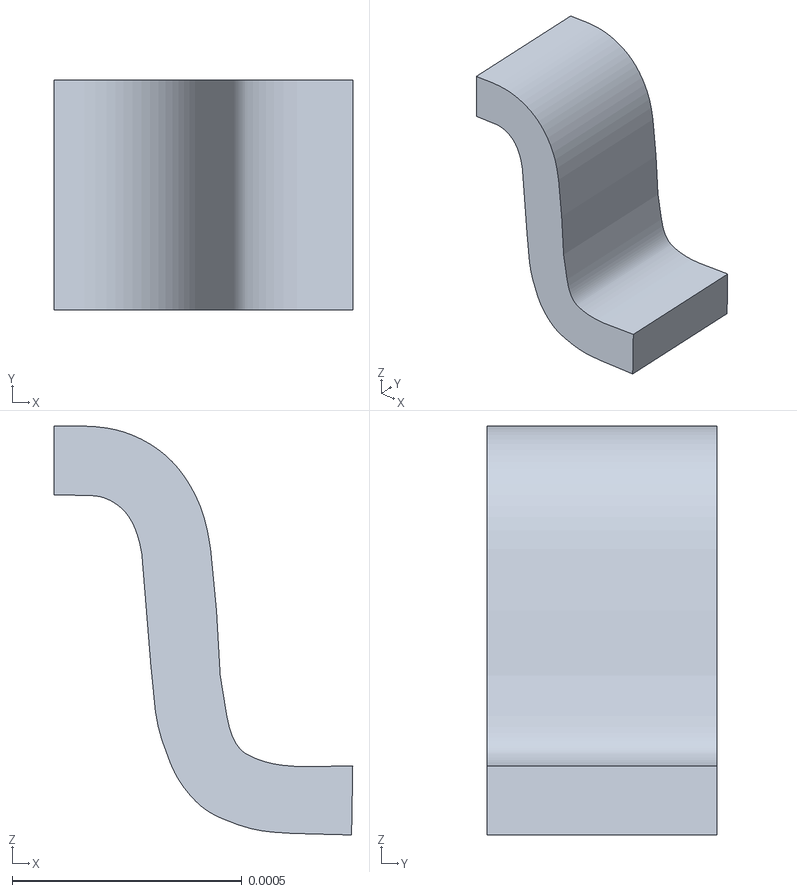
[picture p91: CAD file, 2020-03-03]
deepsoccer_pc/deepsoccer_description/urdf/deepsoccer/sot23-5.stl
0.00065 x 0.0005 x 0.00089
