kimbring2/DeepSoccer/deepsoccer_pc/deepsoccer_description/urdf/deepsoccer/ribbon_cam.stl

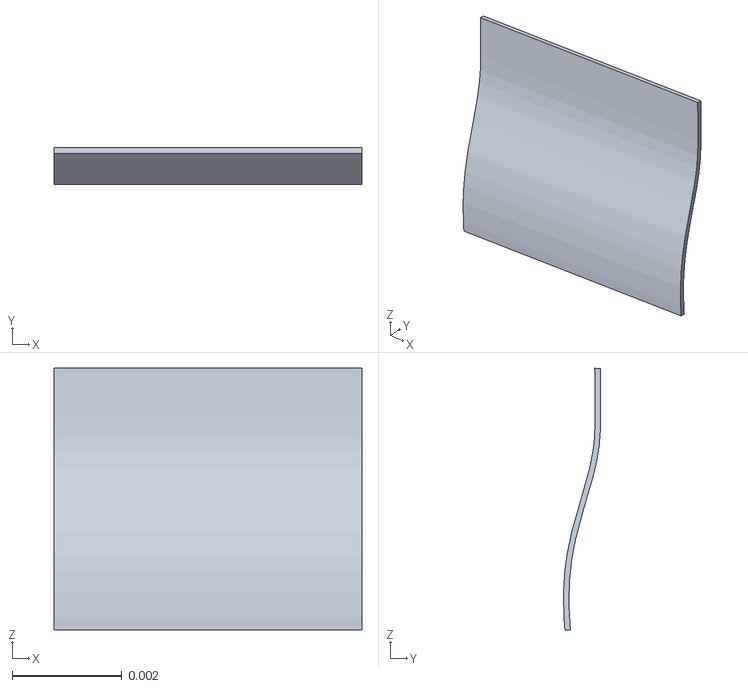
[picture p92: CAD file, 2020-03-03]
deepsoccer_pc/deepsoccer_description/urdf/deepsoccer/ribbon_cam.stl
0.0056 x 0.000673 x 0.00476
