kimbring2/DeepSoccer/deepsoccer_pc/deepsoccer_description/urdf/deepsoccer/kx7_smd_quartz_crystal_resonator_3.2x2.5mm.stl

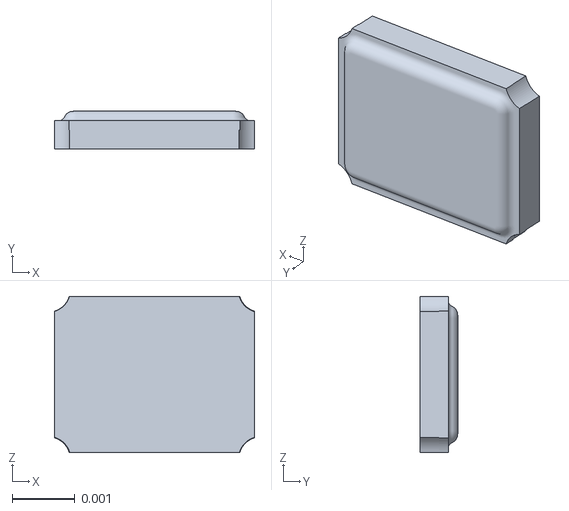
[picture p93: CAD file, 2020-03-03]
deepsoccer_pc/deepsoccer_description/urdf/deepsoccer/kx7_smd_quartz_crystal_resonator_3.2x2.5mm.stl
0.0032 x 0.0006 x 0.0025
