kimbring2/DeepSoccer/deepsoccer_pc/deepsoccer_description/urdf/deepsoccer/4pin_smd.stl

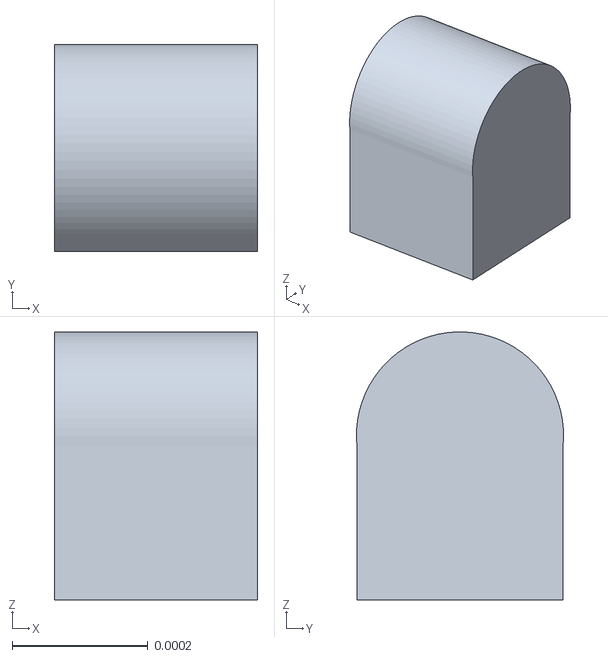
[picture p94: CAD file, 2020-03-03]
deepsoccer_pc/deepsoccer_description/urdf/deepsoccer/4pin_smd.stl
0.0003 x 0.000306 x 0.000395
