kimbring2/DeepSoccer/deepsoccer_pc/deepsoccer_description/urdf/deepsoccer/capc-0805-t0.75-bn.stl

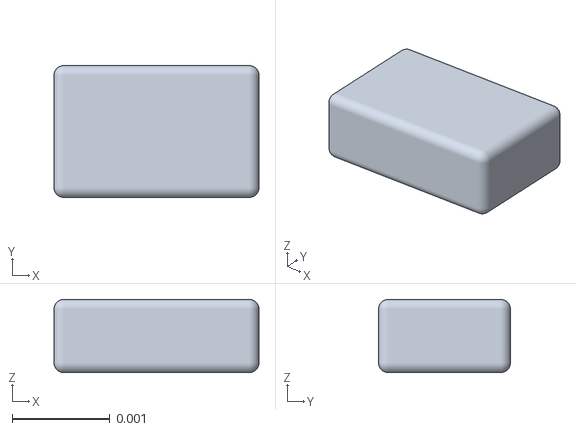
[picture p95: CAD file, 2020-03-03]
deepsoccer_pc/deepsoccer_description/urdf/deepsoccer/capc-0805-t0.75-bn.stl
0.0021 x 0.00135 x 0.00075
