kimbring2/DeepSoccer/deepsoccer_pc/deepsoccer_description/urdf/deepsoccer/resc-0402.stl

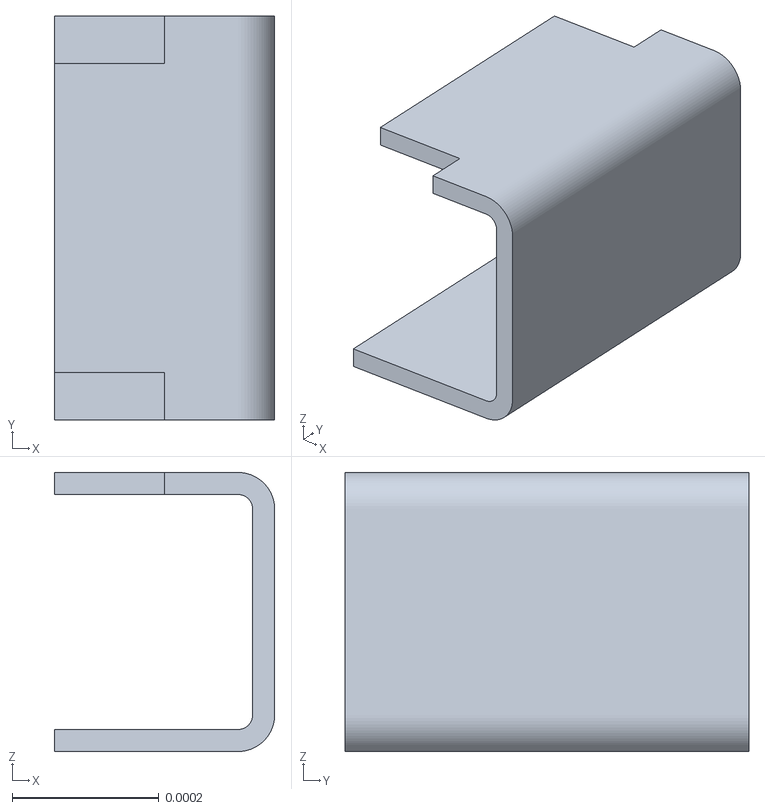
[picture p96: CAD file, 2020-03-03]
deepsoccer_pc/deepsoccer_description/urdf/deepsoccer/resc-0402.stl
0.0003 x 0.00055 x 0.00038
