kimbring2/DeepSoccer/deepsoccer_pc/deepsoccer_description/urdf/deepsoccer/resc-1210.stl

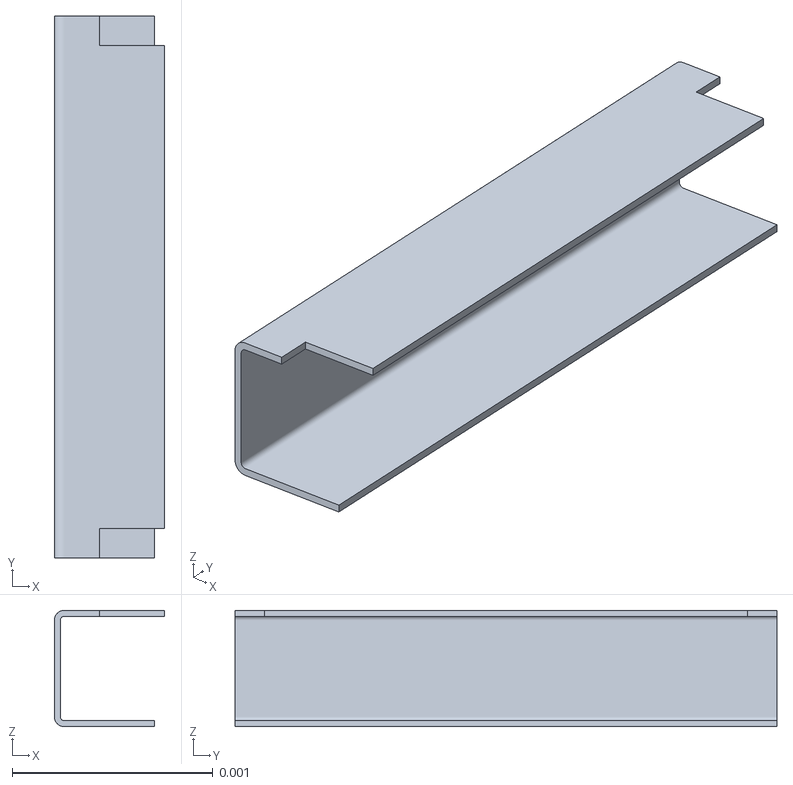
[picture p97: CAD file, 2020-03-03]
deepsoccer_pc/deepsoccer_description/urdf/deepsoccer/resc-1210.stl
0.00055 x 0.0027 x 0.00058
