kimbring2/DeepSoccer/deepsoccer_pc/deepsoccer_description/urdf/deepsoccer/resc-0603.stl

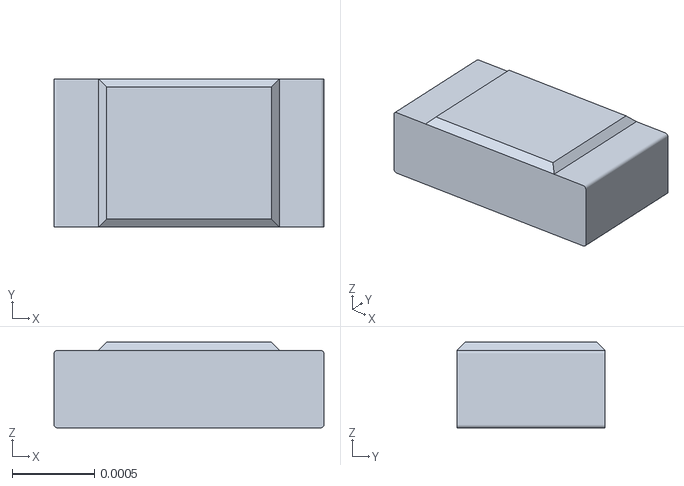
[picture p98: CAD file, 2020-03-03]
deepsoccer_pc/deepsoccer_description/urdf/deepsoccer/resc-0603.stl
0.00164 x 0.0009 x 0.00052
