kimbring2/DeepSoccer/deepsoccer_pc/deepsoccer_description/urdf/deepsoccer/prt0002_1.stl

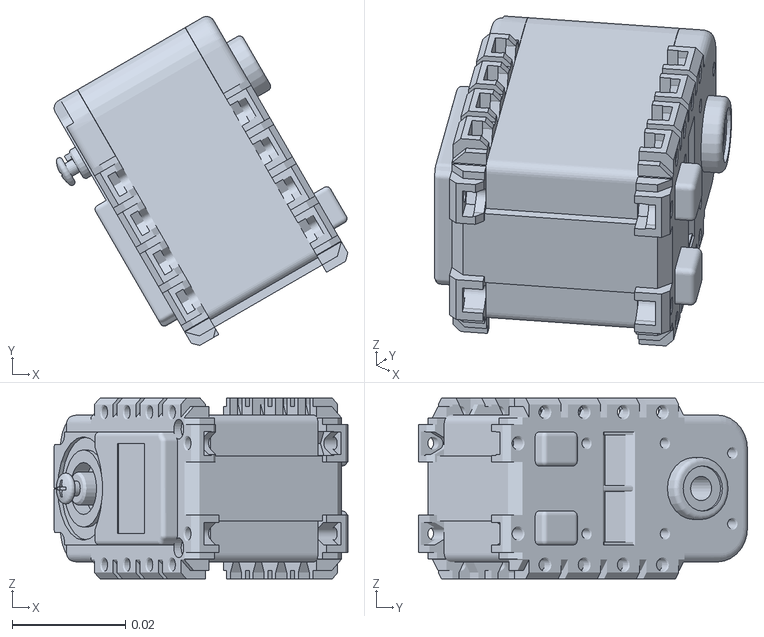
[picture p99: CAD file, 2020-02-02]
deepsoccer_pc/deepsoccer_description/urdf/deepsoccer/prt0002_1.stl
0.052 x 0.0582 x 0.032
