kimbring2/DeepSoccer/deepsoccer_pc/deepsoccer_description/urdf/deepsoccer/m3_l30mm.stl

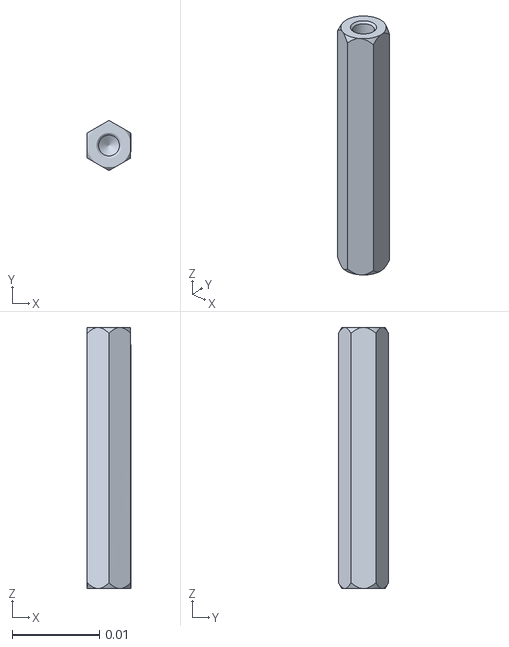
[picture p100: CAD file, 2020-02-02]
deepsoccer_pc/deepsoccer_description/urdf/deepsoccer/m3_l30mm.stl
0.005 x 0.00577 x 0.03
