kimbring2/DeepSoccer/deepsoccer_pc/deepsoccer_description/urdf/deepsoccer/____.step.stl

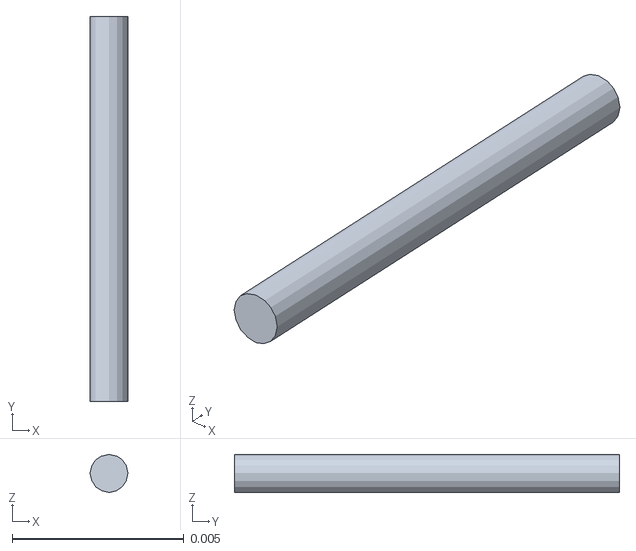
[picture p101: CAD file, 2020-02-02]
deepsoccer_pc/deepsoccer_description/urdf/deepsoccer/____.step.stl
0.00111 x 0.0112 x 0.00111
