kimbring2/DeepSoccer/deepsoccer_pc/deepsoccer_description/urdf/deepsoccer/gearbox.stl

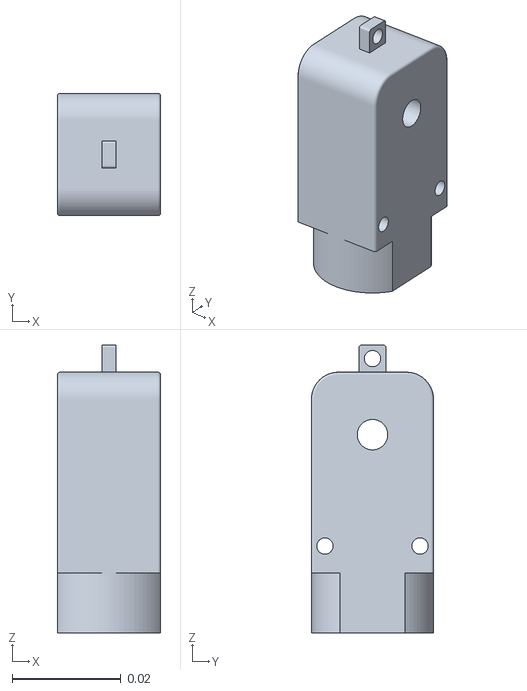
[picture p102: CAD file, 2020-02-02]
deepsoccer_pc/deepsoccer_description/urdf/deepsoccer/gearbox.stl
0.019 x 0.0225 x 0.053
