kimbring2/DeepSoccer/deepsoccer_pc/deepsoccer_description/urdf/deepsoccer/output_shaft.stl

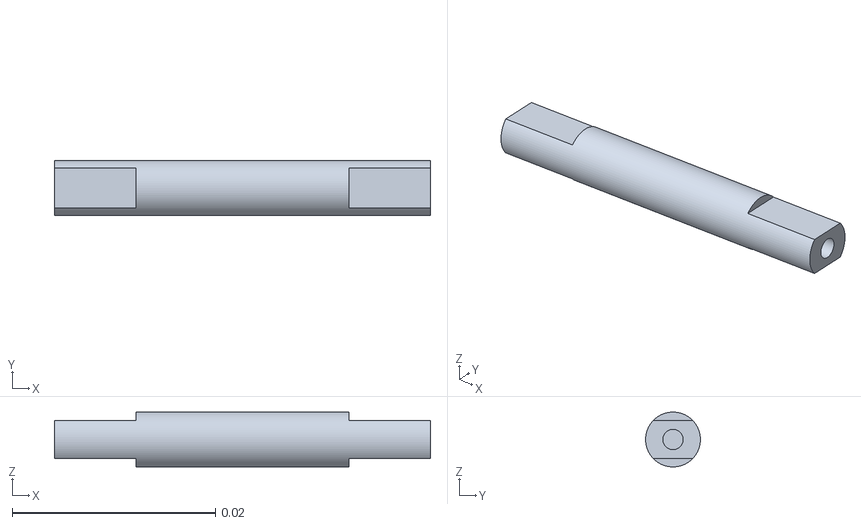
[picture p103: CAD file, 2020-02-02]
deepsoccer_pc/deepsoccer_description/urdf/deepsoccer/output_shaft.stl
0.037 x 0.0054 x 0.0054
