kimbring2/DeepSoccer/deepsoccer_pc/deepsoccer_description/urdf/deepsoccer/antennae.step.stl

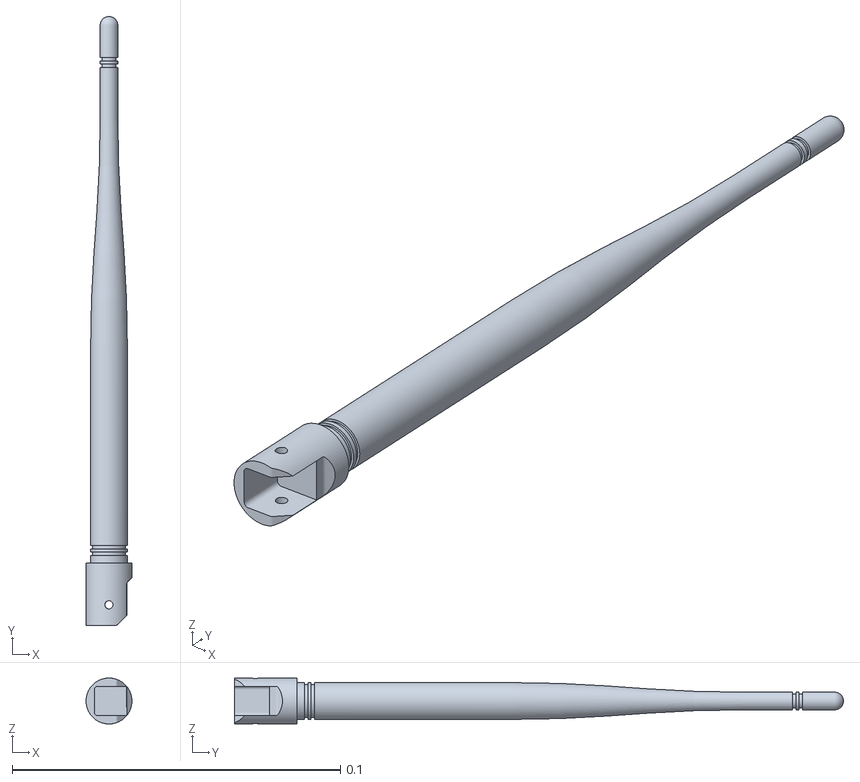
[picture p104: CAD file, 2020-02-02]
deepsoccer_pc/deepsoccer_description/urdf/deepsoccer/antennae.step.stl
0.014 x 0.186 x 0.014
