kimbring2/DeepSoccer/deepsoccer_pc/deepsoccer_description/urdf/deepsoccer/____msbr_5.stl

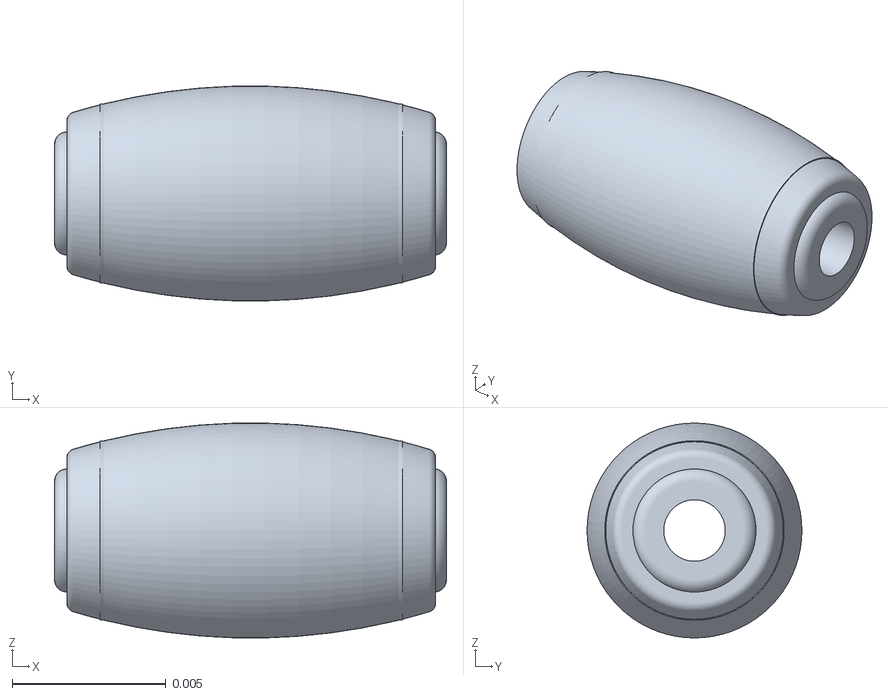
[picture p107: CAD file, 2020-02-02]
deepsoccer_pc/deepsoccer_description/urdf/deepsoccer/____msbr_5.stl
0.0127 x 0.00699 x 0.00699
