kimbring2/DeepSoccer/deepsoccer_pc/deepsoccer_description/urdf/deepsoccer/pcb.step.stl

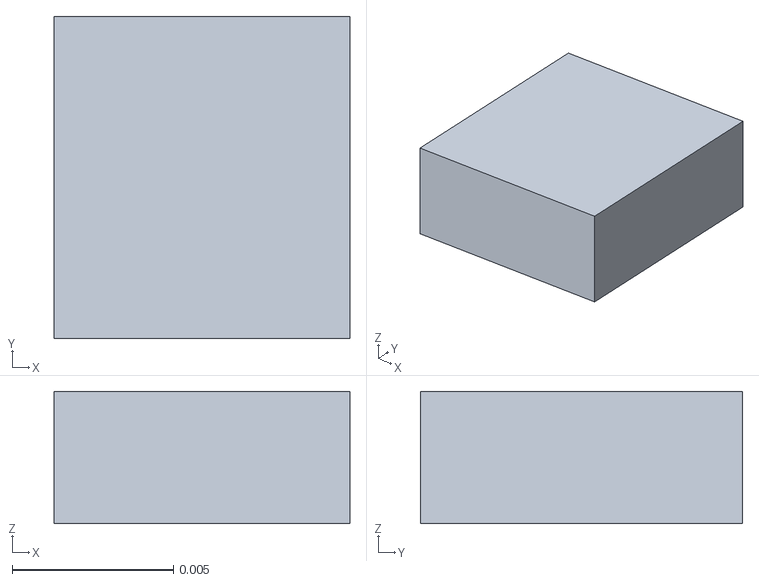
[picture p108: CAD file, 2020-02-02]
deepsoccer_pc/deepsoccer_description/urdf/deepsoccer/pcb.step.stl
0.00919 x 0.01 x 0.0041
