kimbring2/DeepSoccer/deepsoccer_pc/deepsoccer_description/urdf/deepsoccer/antenna_hub.step.stl

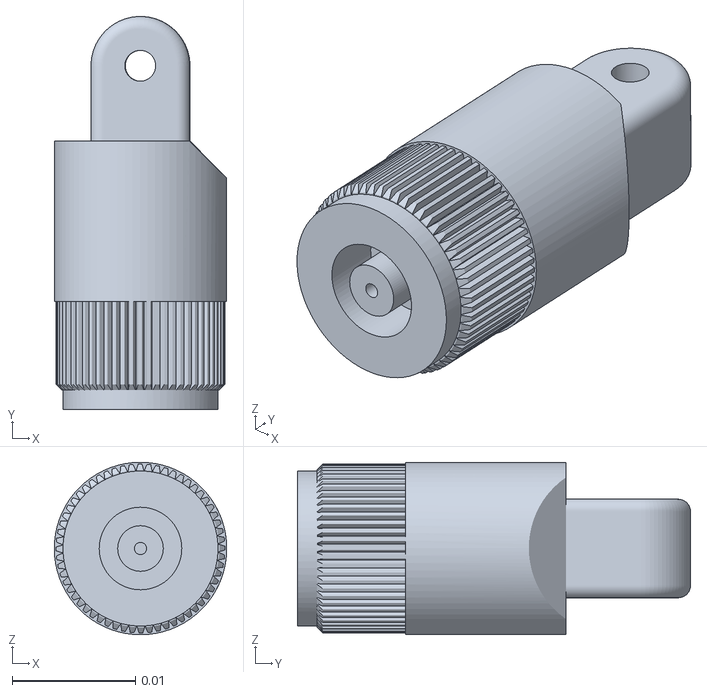
[picture p109: CAD file, 2020-02-02]
deepsoccer_pc/deepsoccer_description/urdf/deepsoccer/antenna_hub.step.stl
0.014 x 0.0319 x 0.014
