kimbring2/DeepSoccer/deepsoccer_pc/deepsoccer_description/urdf/deepsoccer/prt0002.stl

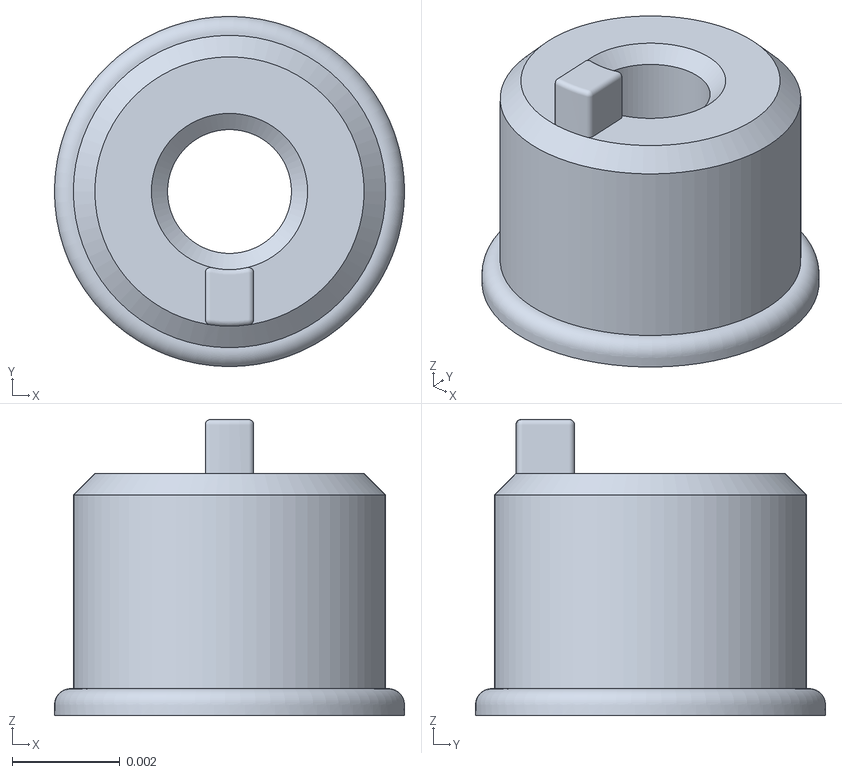
[picture p110: CAD file, 2020-01-19]
deepsoccer_pc/deepsoccer_description/urdf/deepsoccer/prt0002.stl
0.0065 x 0.0065 x 0.0055
