kimbring2/DeepSoccer/deepsoccer_pc/deepsoccer_description/urdf/deepsoccer/solenoid_case_2.stl

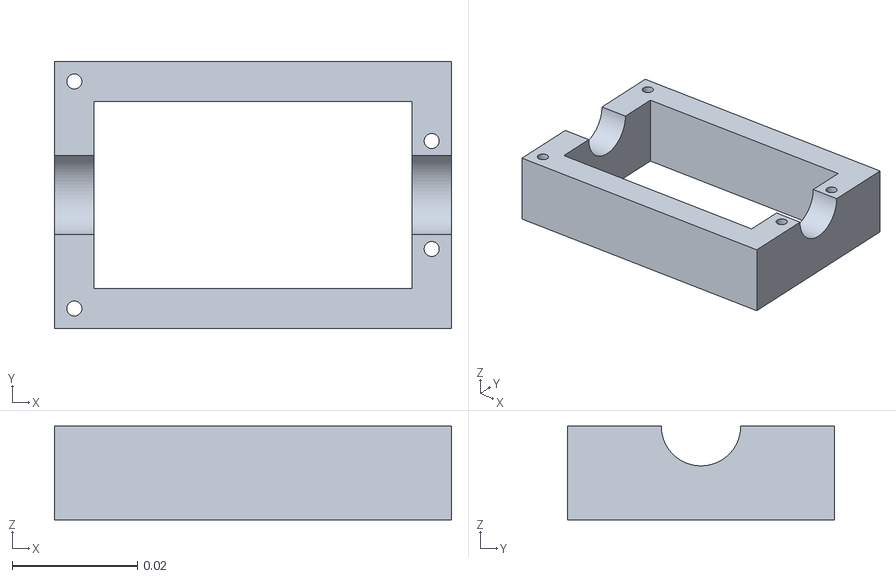
[picture p111: CAD file, 2020-01-19]
deepsoccer_pc/deepsoccer_description/urdf/deepsoccer/solenoid_case_2.stl
0.0635 x 0.0427 x 0.015
