kimbring2/DeepSoccer/deepsoccer_pc/deepsoccer_description/urdf/deepsoccer/prt0003.stl

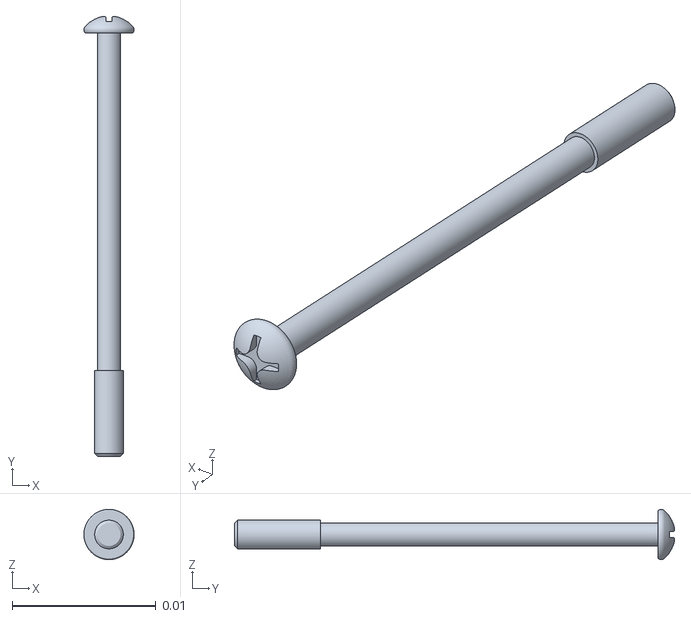
[picture p112: CAD file, 2020-01-19]
deepsoccer_pc/deepsoccer_description/urdf/deepsoccer/prt0003.stl
0.0035 x 0.0306 x 0.0035
