kimbring2/DeepSoccer/deepsoccer_pc/deepsoccer_description/urdf/deepsoccer/prt0001.stl

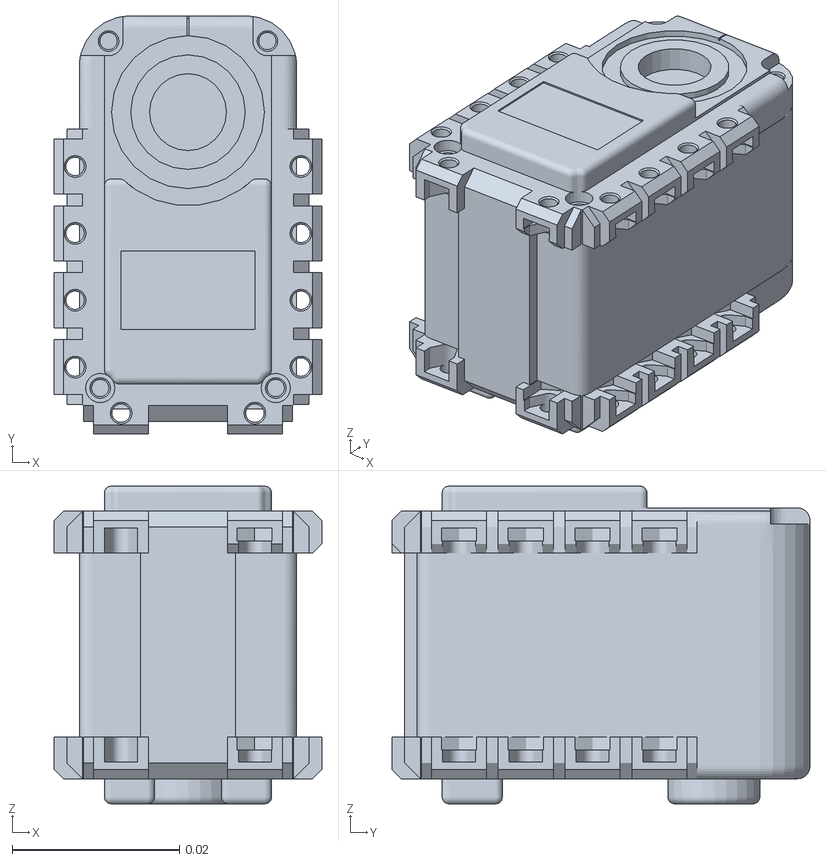
[picture p113: CAD file, 2020-01-19]
deepsoccer_pc/deepsoccer_description/urdf/deepsoccer/prt0001.stl
0.032 x 0.05 x 0.038
