kimbring2/DeepSoccer/deepsoccer_pc/deepsoccer_description/urdf/deepsoccer/roller_core.stl

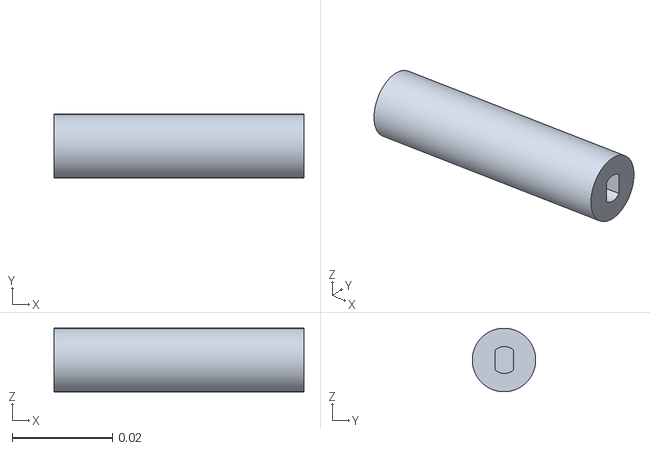
[picture p114: CAD file, 2020-01-19]
deepsoccer_pc/deepsoccer_description/urdf/deepsoccer/roller_core.stl
0.05 x 0.0127 x 0.0127
