kimbring2/DeepSoccer/deepsoccer_pc/deepsoccer_description/urdf/deepsoccer/1.14_tft_ips_-_13p_-_reverse_mount.step.stl

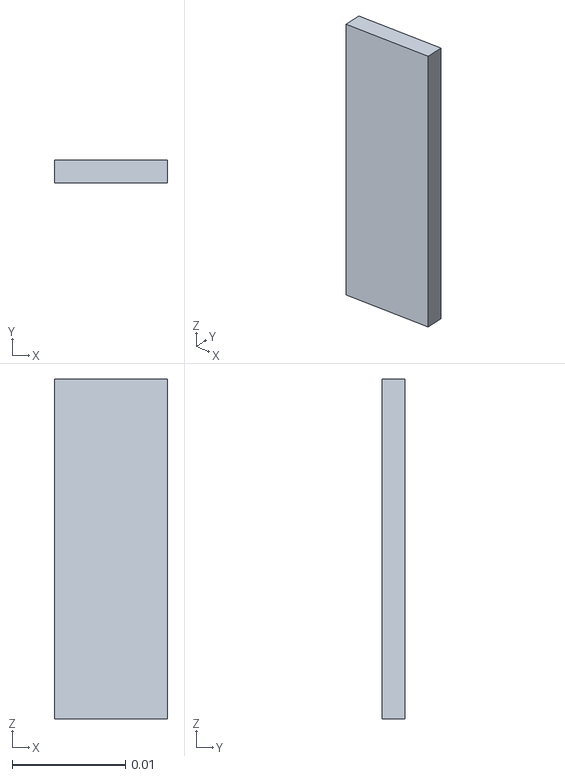
[picture p117: CAD file, 2020-01-19]
deepsoccer_pc/deepsoccer_description/urdf/deepsoccer/1.14_tft_ips_-_13p_-_reverse_mount.step.stl
0.01 x 0.002 x 0.03
