kimbring2/DeepSoccer/deepsoccer_pc/deepsoccer_description/urdf/deepsoccer/12v.step.stl

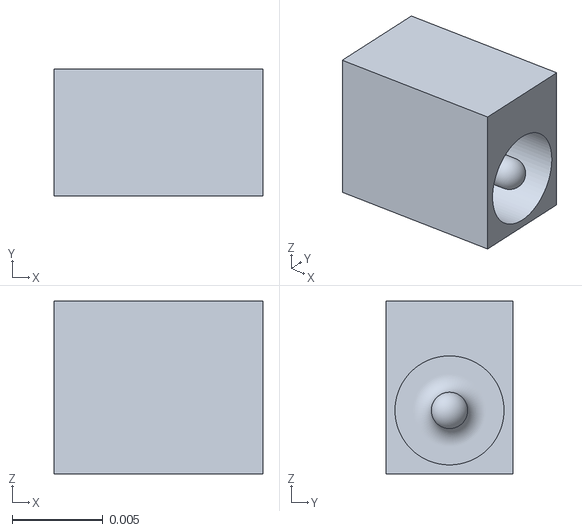
[picture p118: CAD file, 2020-01-19]
deepsoccer_pc/deepsoccer_description/urdf/deepsoccer/12v.step.stl
0.0115 x 0.007 x 0.0095
