kimbring2/DeepSoccer/deepsoccer_pc/deepsoccer_description/urdf/deepsoccer/mx-12w_horn.stl

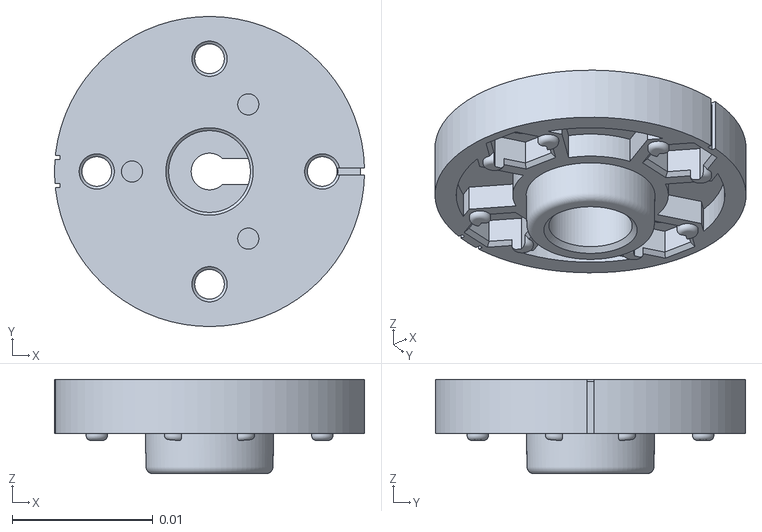
[picture p120: CAD file, 2020-01-19]
deepsoccer_pc/deepsoccer_description/urdf/deepsoccer/mx-12w_horn.stl
0.022 x 0.022 x 0.0067
