kimbring2/DeepSoccer/deepsoccer_jetson/scripts/deepsoccer_lidar.py

#!/usr/bin/env python
import rospy
import serial
import time
from std_msgs.msg import String


def getTFminiData():
    #time.sleep(0.1)
    count = ser.in_waiting
    #print("count: " + str(count))
    distance = None
    if count > 8:
        recv = ser.read(9)
        ser.reset_input_buffer()
            
        # type(recv), 'str' in python2(recv[0] = 'Y'), 'bytes' in python3(recv[0] = 89)
        # type(recv[0]), 'str' in python2, 'int' in python3
        if recv[0] == 0x59 and recv[1] == 0x59:
            distance = recv[2] + recv[3] * 256
            strength = recv[4] + recv[5] * 256
            #print('(', distance, ',', strength, ')')

        ser.reset_input_buffer()

        #python3
        if recv[0] == 'Y' and recv[1] == 'Y': #python2
            lowD = int(recv[2].encode('hex'), 16)
            highD = int(recv[3].encode('hex'), 16)
            lowS = int(recv[4].encode('hex'), 16)
            highS = int(recv[5].encode('hex'), 16)
            distance = lowD + highD * 256
            strength = lowS + highS * 256
            #print(distance, strength)
                
    return distance
    
    
# initialization
if __name__ == '__main__':
    # UART Setup:
	# Board pin-numbering scheme
    ser = serial.Serial("/dev/ttyTHS0", 115200)
    
	# setup ros node
    pub = rospy.Publisher('deepsoccer_lidar', String, queue_size=10)
    rospy.init_node('deepsoccer_lidar')
    r = rospy.Rate(200) # 10hz
    while not rospy.is_shutdown():
        lidar_value = getTFminiData()
        
        if lidar_value != None:
            pub.publish(str(lidar_value))
            
        r.sleep()
